tebl/C64-JoyKEY/gallery/2020-12-01 23.58.18.jpg

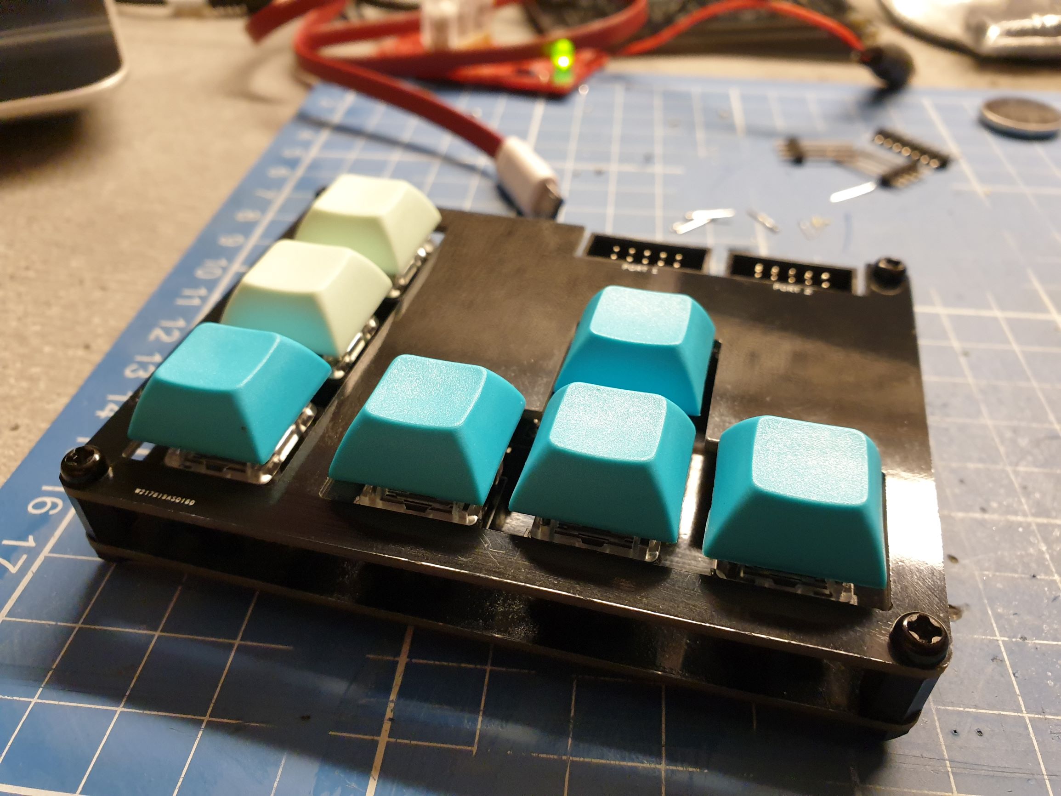
gallery/2020-12-01 23.58.18.jpg
