tebl/C64-JoyKEY/gallery/2020-12-05 21.04.29.jpg

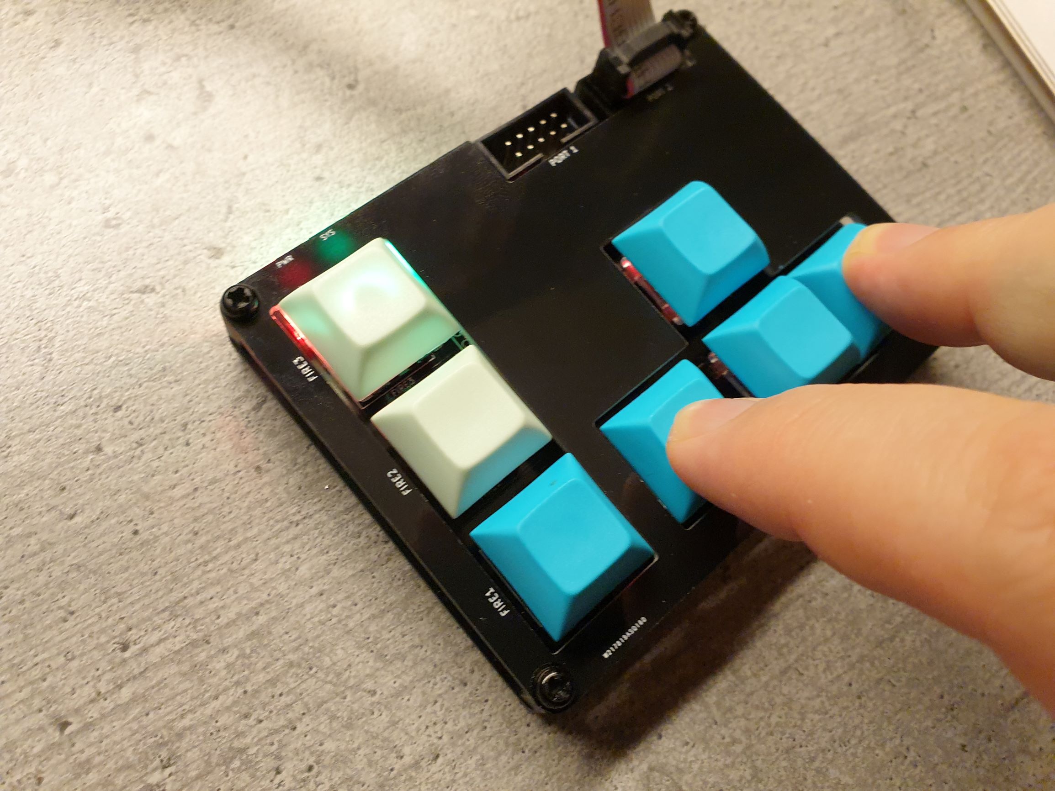
gallery/2020-12-05 21.04.29.jpg
