tebl/C64-JoyKEY/gallery/2020-12-06 00.33.15.jpg

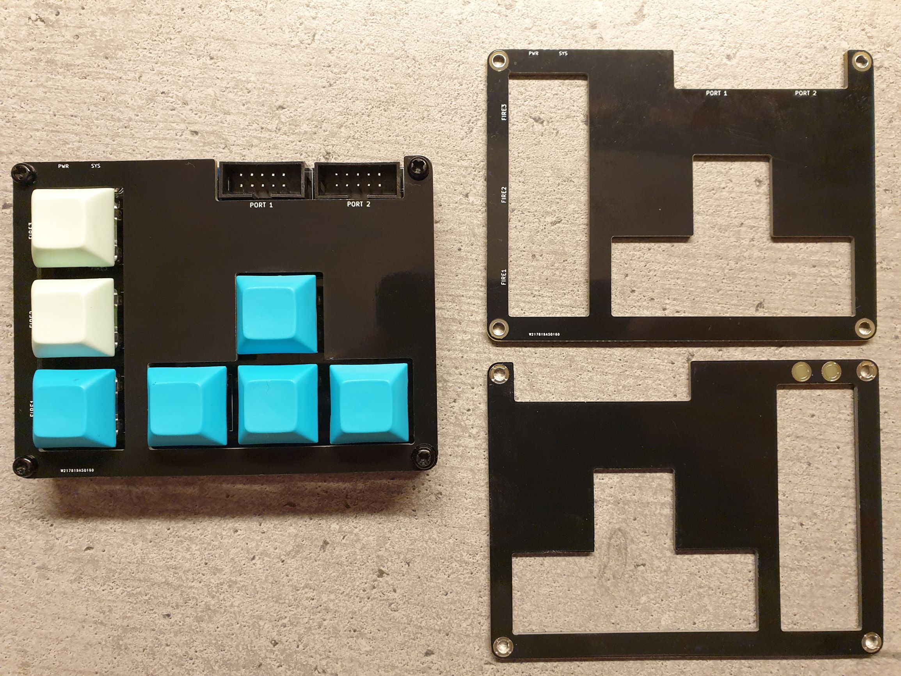
gallery/2020-12-06 00.33.15.jpg
