tebl/C64-JoyKEY/gallery/2021-01-07 00.18.26.jpg

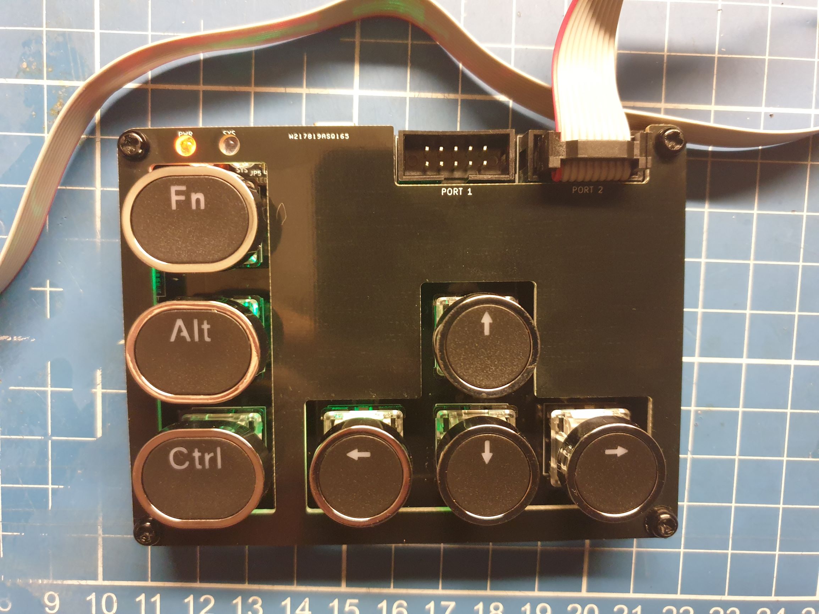
gallery/2021-01-07 00.18.26.jpg
