tebl/C64-JoyKEY/gallery/2021-01-18 20.31.05.jpg

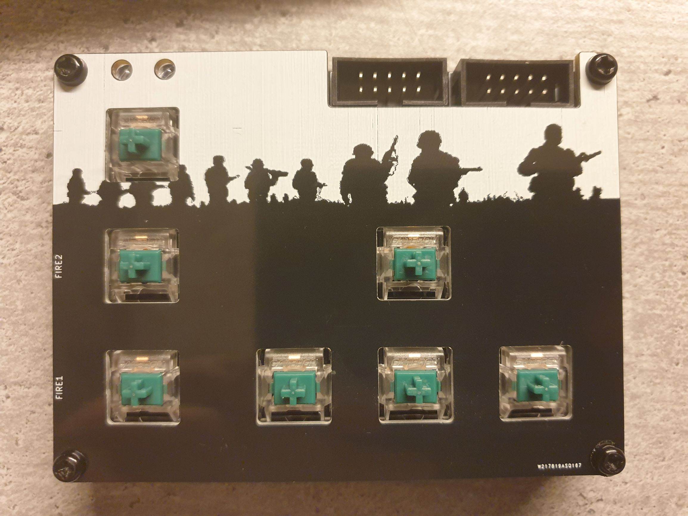
gallery/2021-01-18 20.31.05.jpg
