tebl/C64-JoyKEY/gallery/2021-01-18 20.33.16.jpg

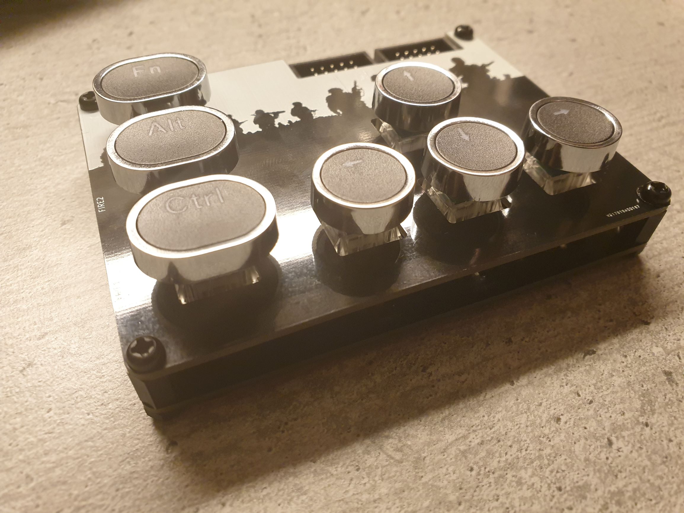
gallery/2021-01-18 20.33.16.jpg
