tebl/C64-JoyKEY/gallery/2021-01-26 00.23.01.jpg

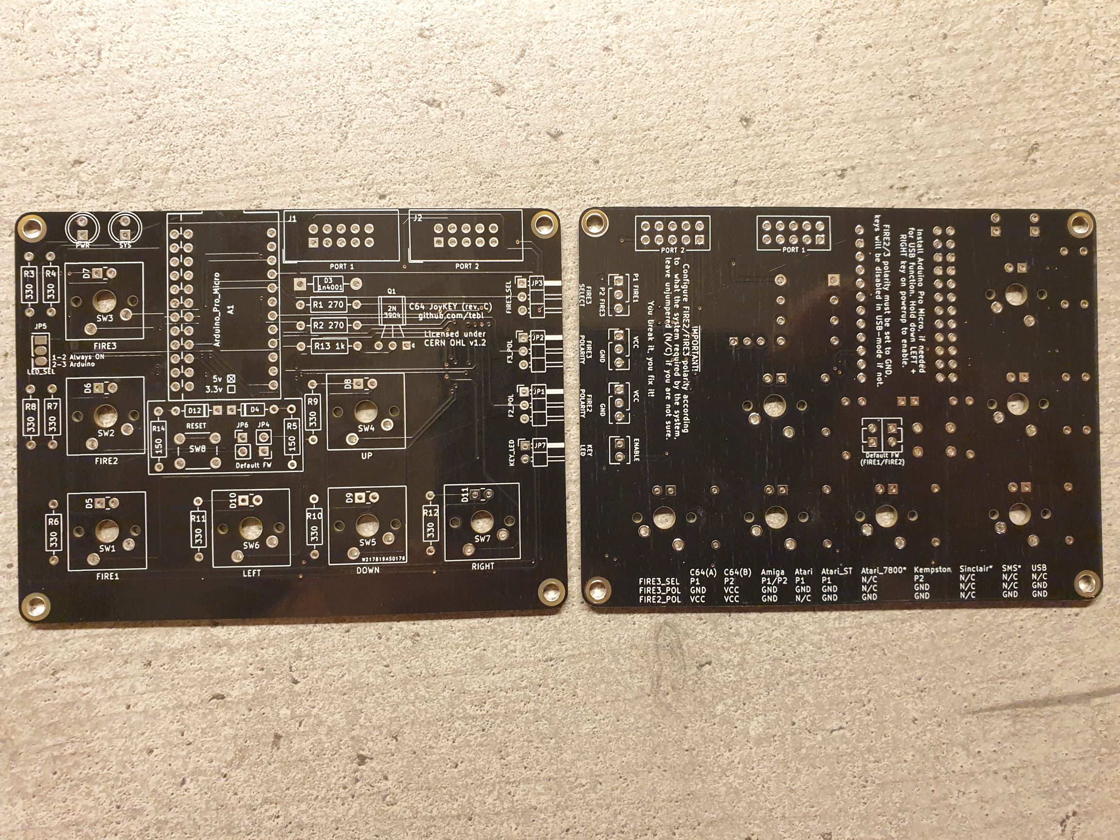
gallery/2021-01-26 00.23.01.jpg
