tebl/C64-JoyKEY/gallery/2021-01-26 03.19.31.jpg

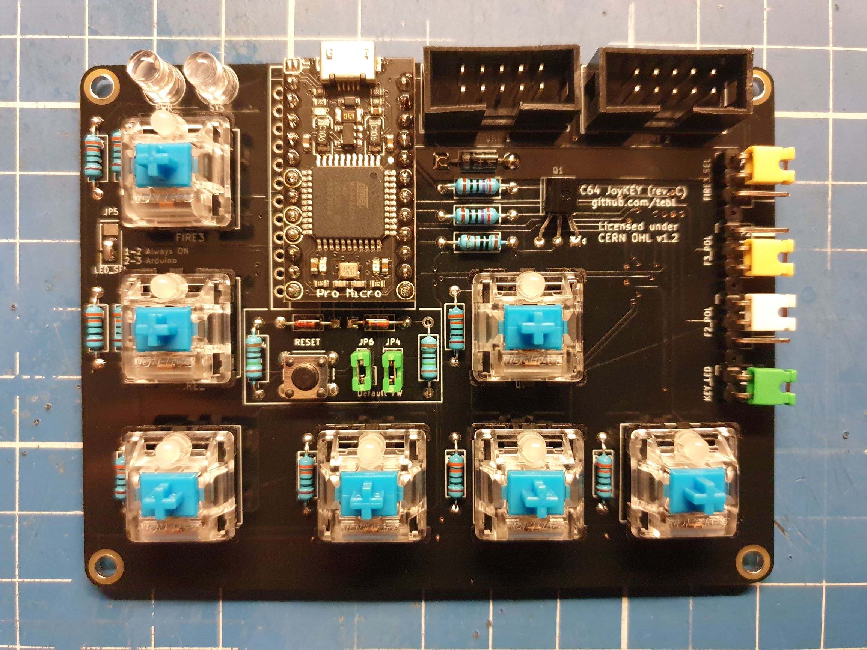
gallery/2021-01-26 03.19.31.jpg
