tebl/C64-JoyKEY/gallery/2021-02-02 23.40.10.jpg

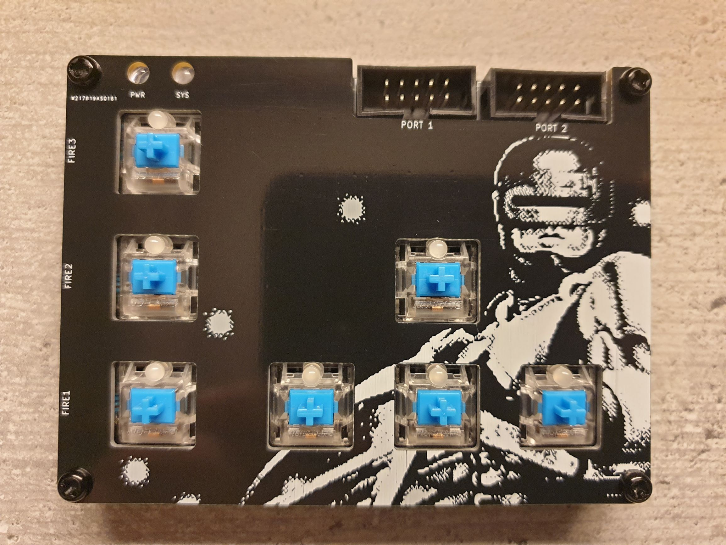
gallery/2021-02-02 23.40.10.jpg
