tebl/C64-JoyKEY/gallery/2021-02-02 23.41.32.jpg

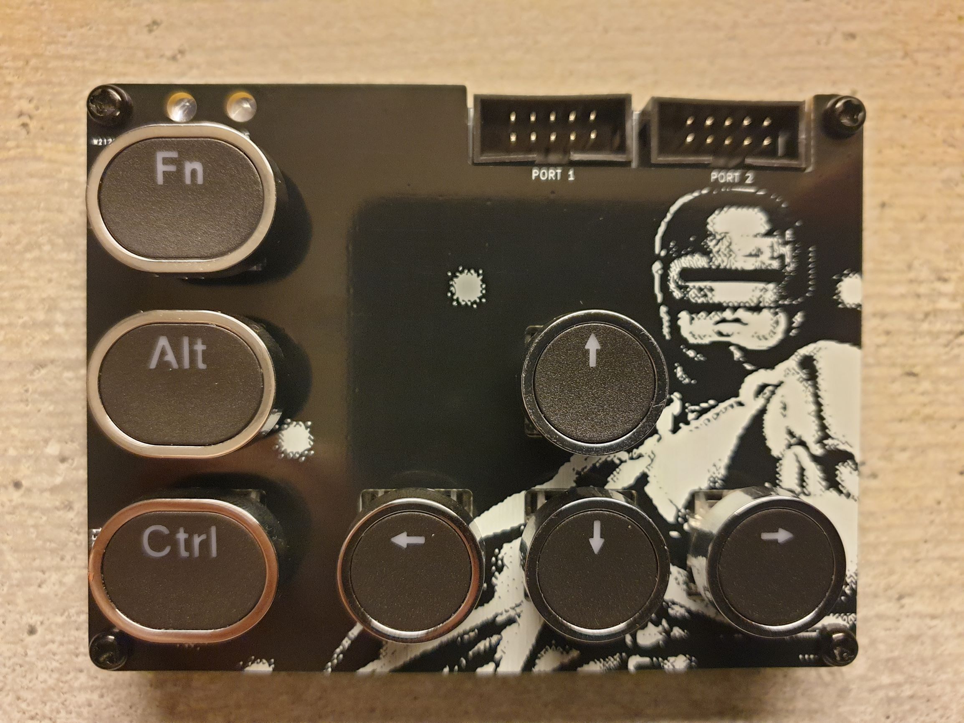
gallery/2021-02-02 23.41.32.jpg
