tebl/C64-JoyKEY/gallery/2021-02-03 00.52.26.jpg

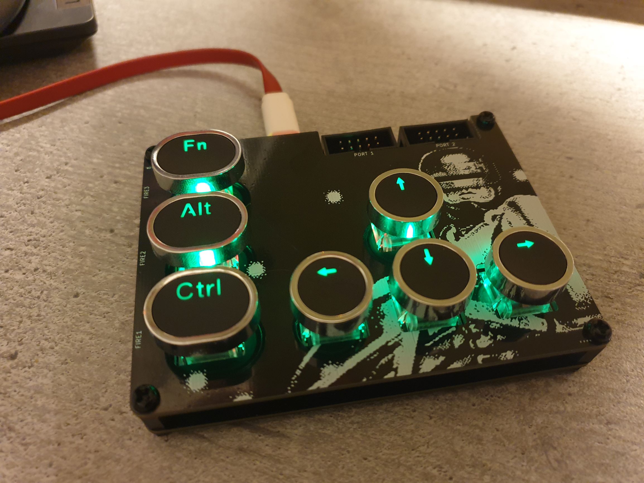
gallery/2021-02-03 00.52.26.jpg
