tebl/C64-JoyKEY/gallery/2021-03-08 21.28.13.jpg

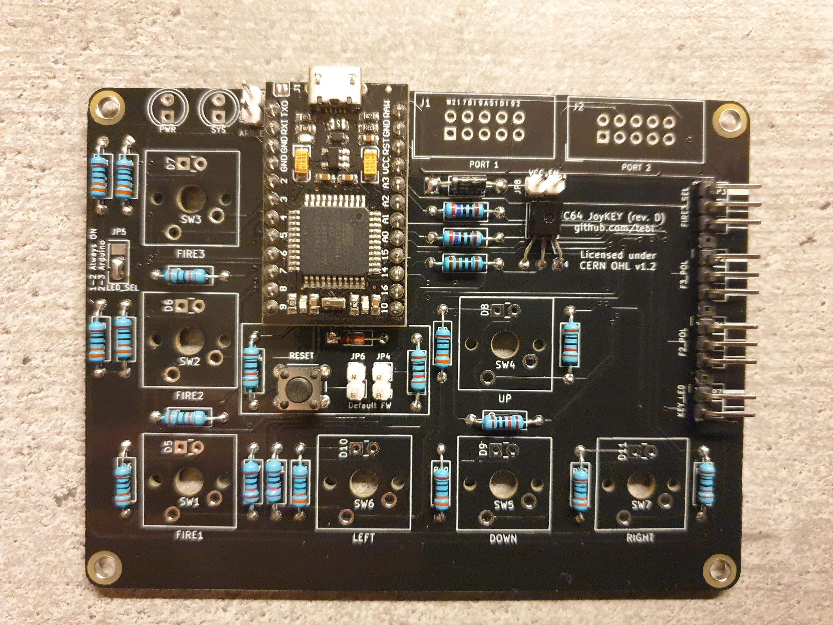
gallery/2021-03-08 21.28.13.jpg
