tebl/C64-JoyKEY/gallery/2021-03-09 01.28.27.jpg

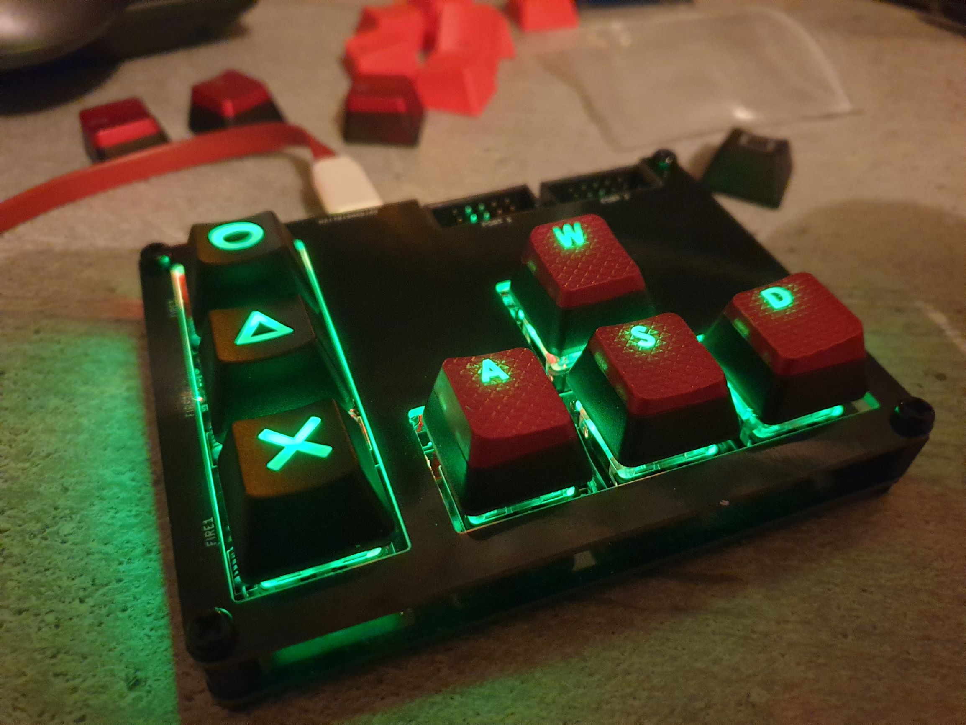
gallery/2021-03-09 01.28.27.jpg
