tebl/C64-JoyKEY/gallery/2021-03-09 01.42.43.jpg

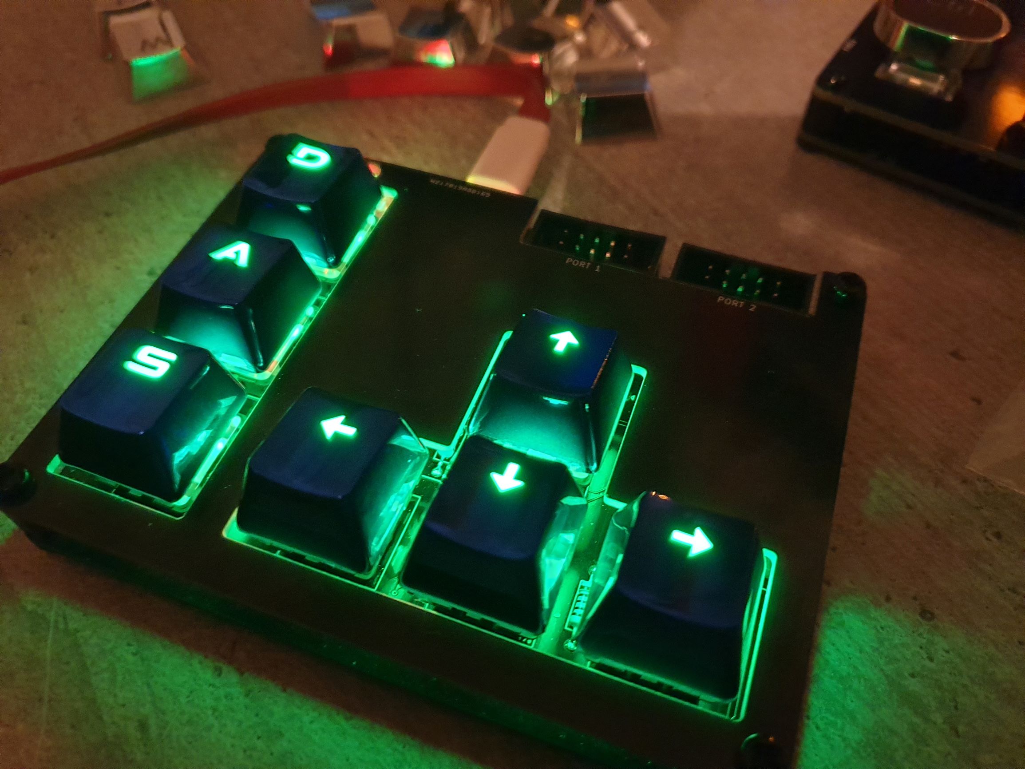
gallery/2021-03-09 01.42.43.jpg
