tebl/C64-JoyKEY/gallery/2021-03-10 20.38.43.jpg

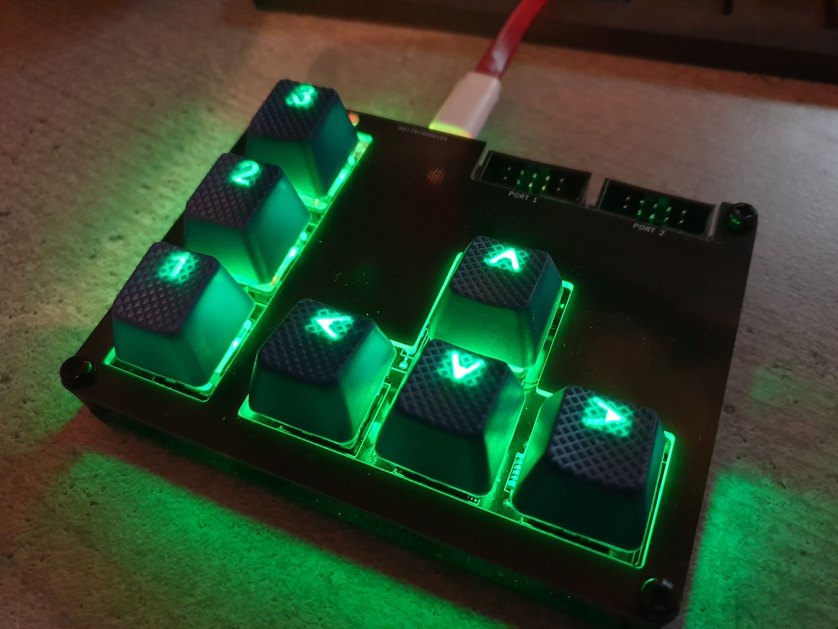
gallery/2021-03-10 20.38.43.jpg
