tebl/C64-JoyKEY/gallery/2021-03-30 01.16.27.jpg

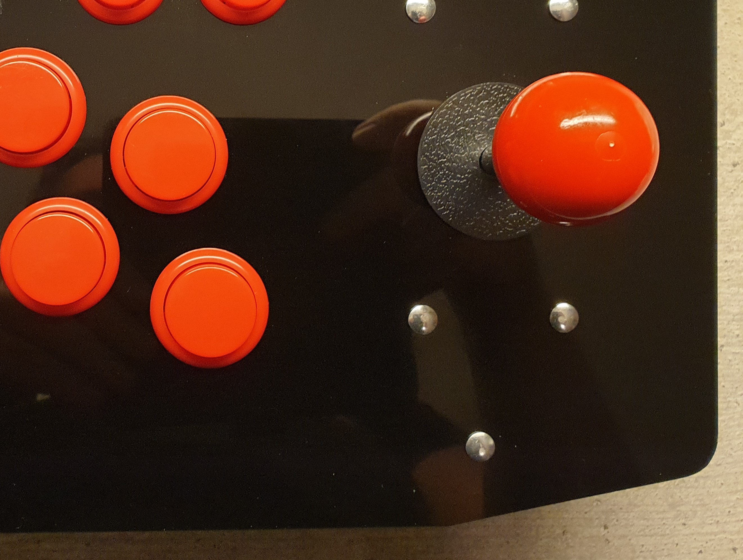
gallery/2021-03-30 01.16.27.jpg
