tebl/C64-JoyKEY/gallery/2021-04-14 00.00.06.jpg

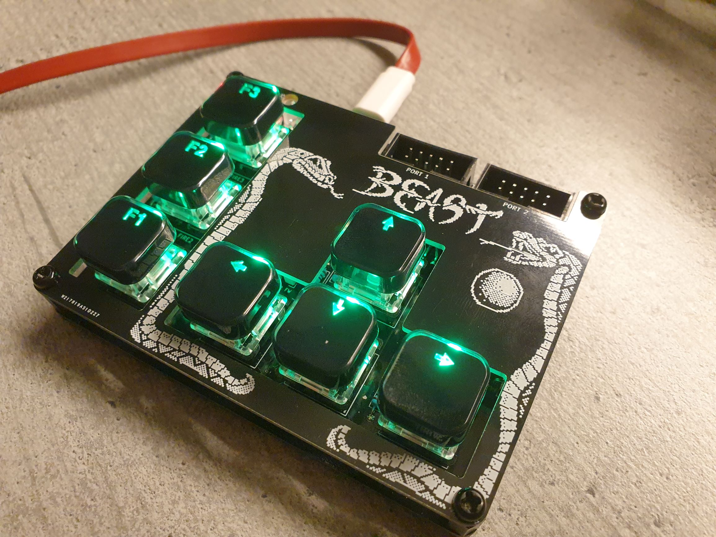
gallery/2021-04-14 00.00.06.jpg
