tebl/C64-JoyKEY/gallery/2022-02-19 15.27.10.jpg

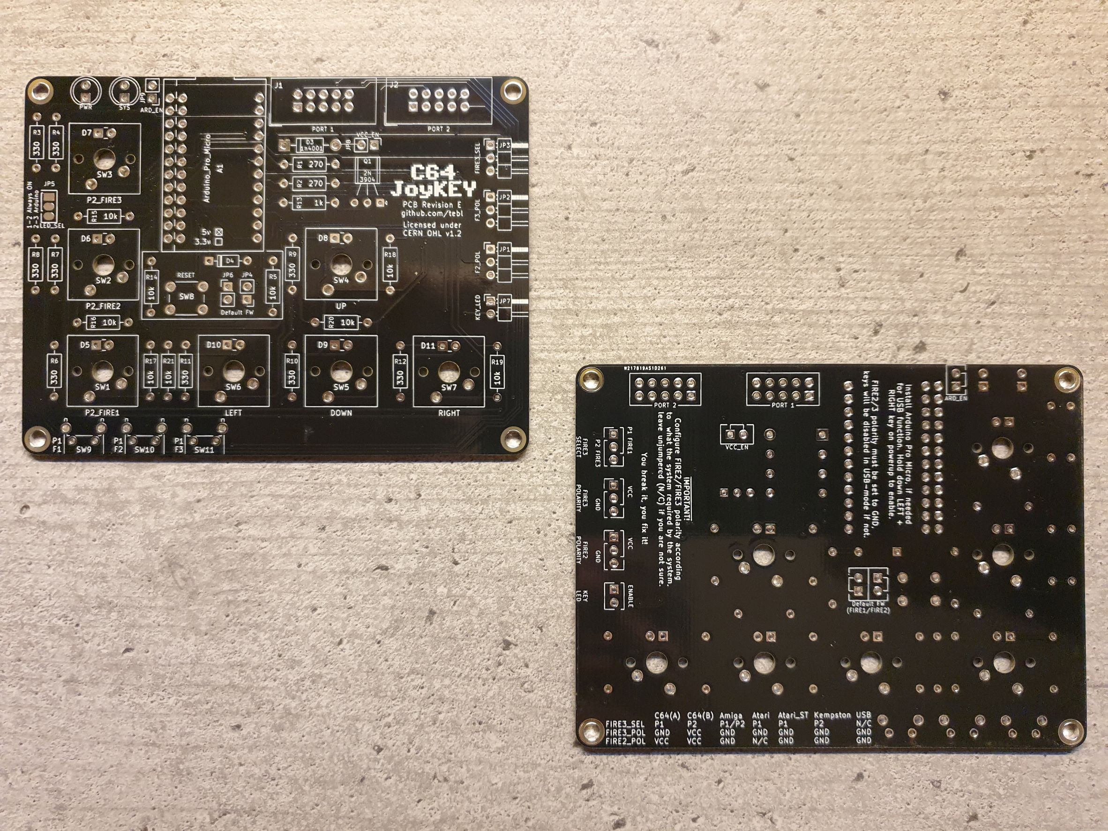
gallery/2022-02-19 15.27.10.jpg
