tebl/C64-JoyKEY/gallery/2022-02-19 16.09.59.jpg

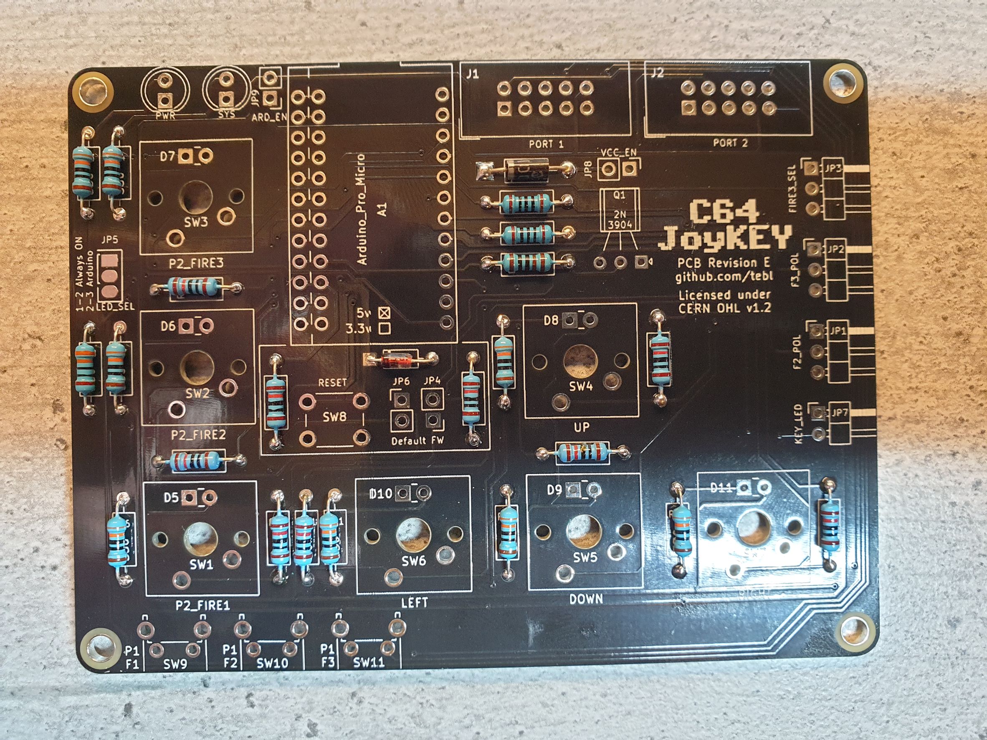
gallery/2022-02-19 16.09.59.jpg
