tebl/C64-JoyKEY/gallery/2022-02-19 16.12.47.jpg

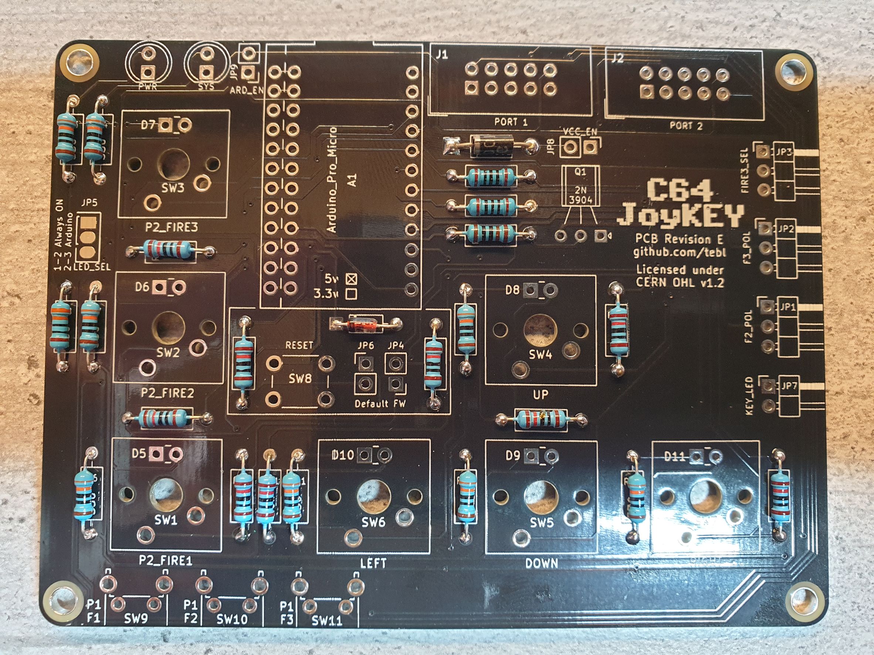
gallery/2022-02-19 16.12.47.jpg
