tebl/C64-JoyKEY/gallery/2022-02-19 16.19.15.jpg

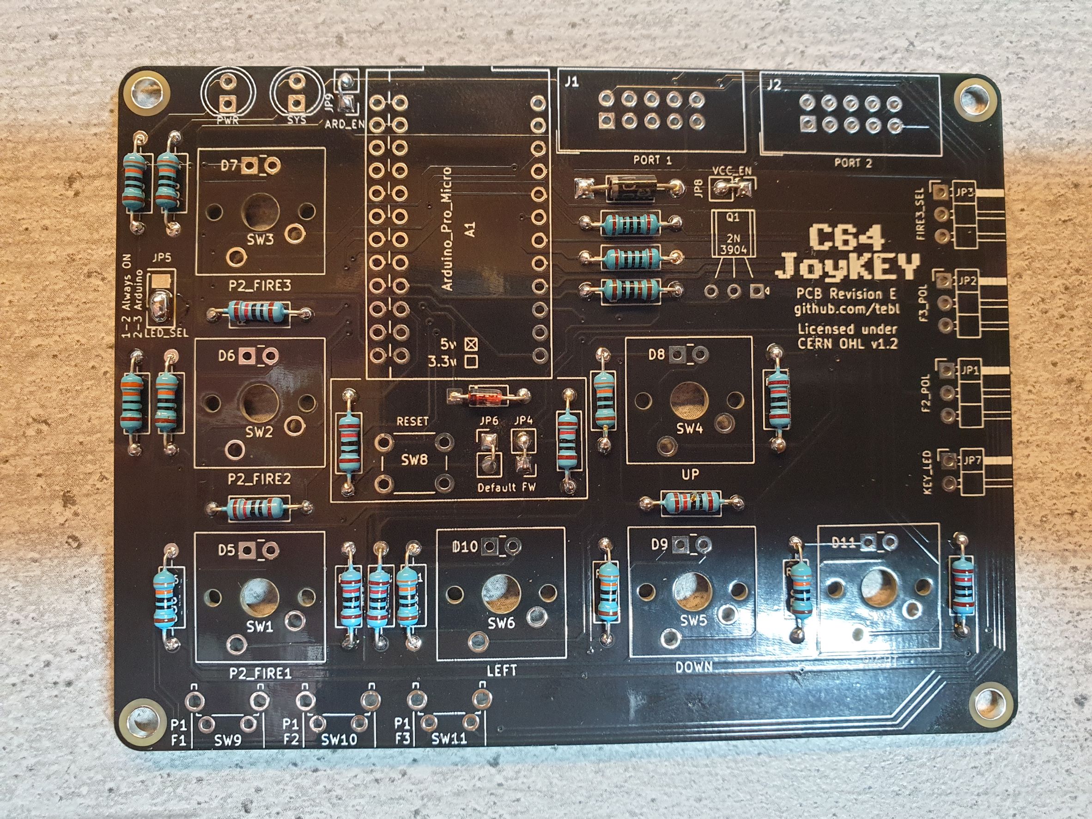
gallery/2022-02-19 16.19.15.jpg
