tebl/C64-JoyKEY/gallery/2022-02-19 16.20.50.jpg

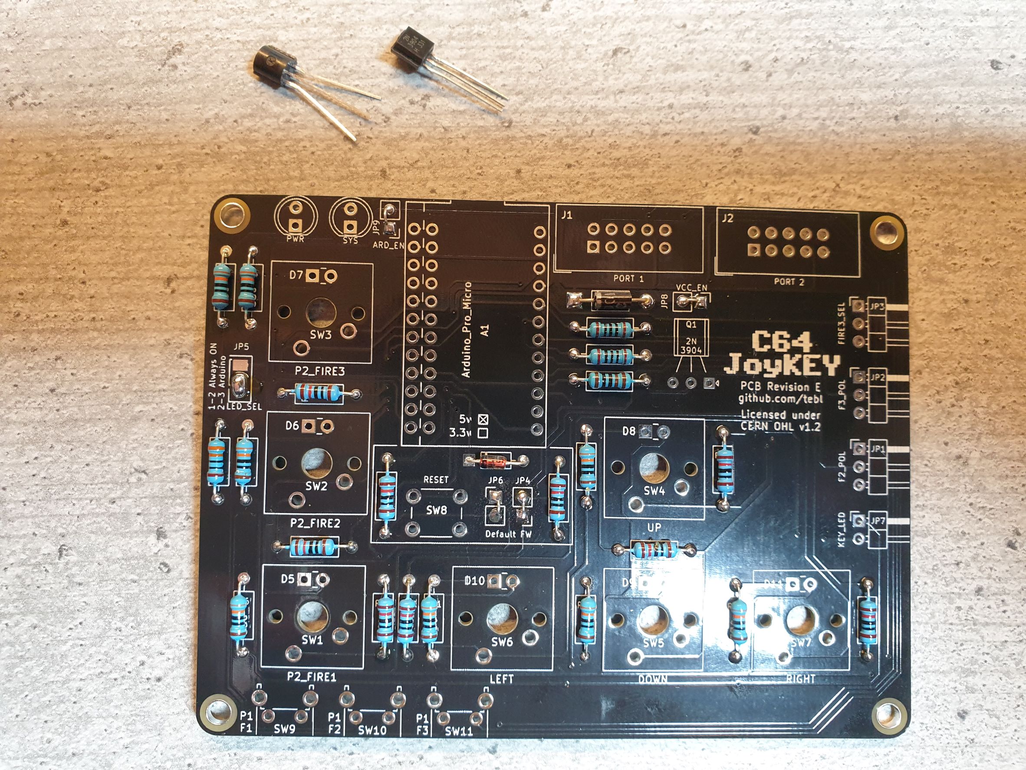
gallery/2022-02-19 16.20.50.jpg
