tebl/C64-JoyKEY/gallery/2022-02-19 16.23.03.jpg

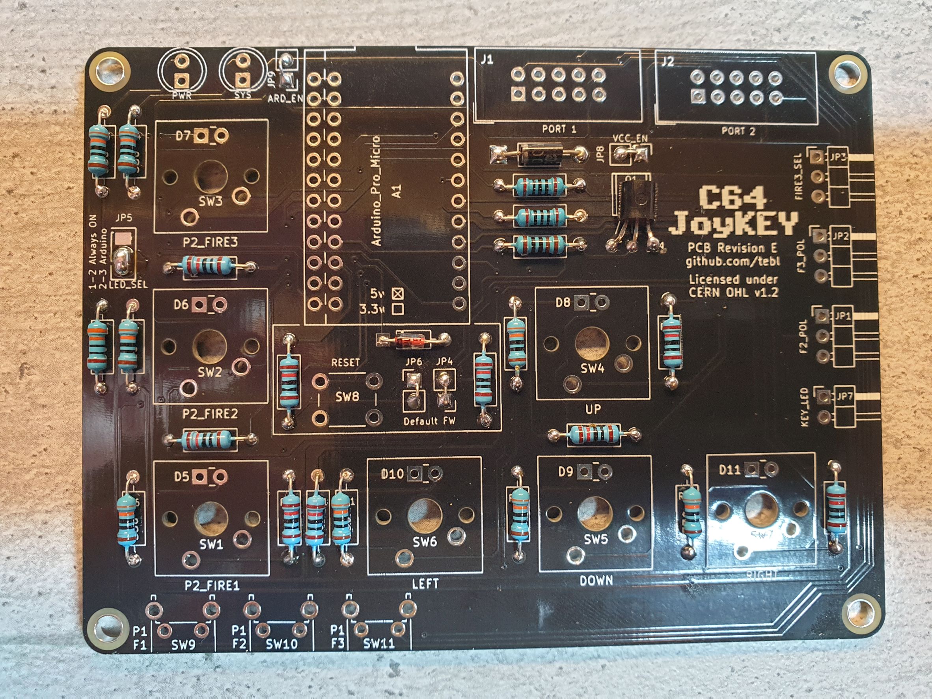
gallery/2022-02-19 16.23.03.jpg
