tebl/C64-JoyKEY/gallery/2022-02-19 16.27.23.jpg

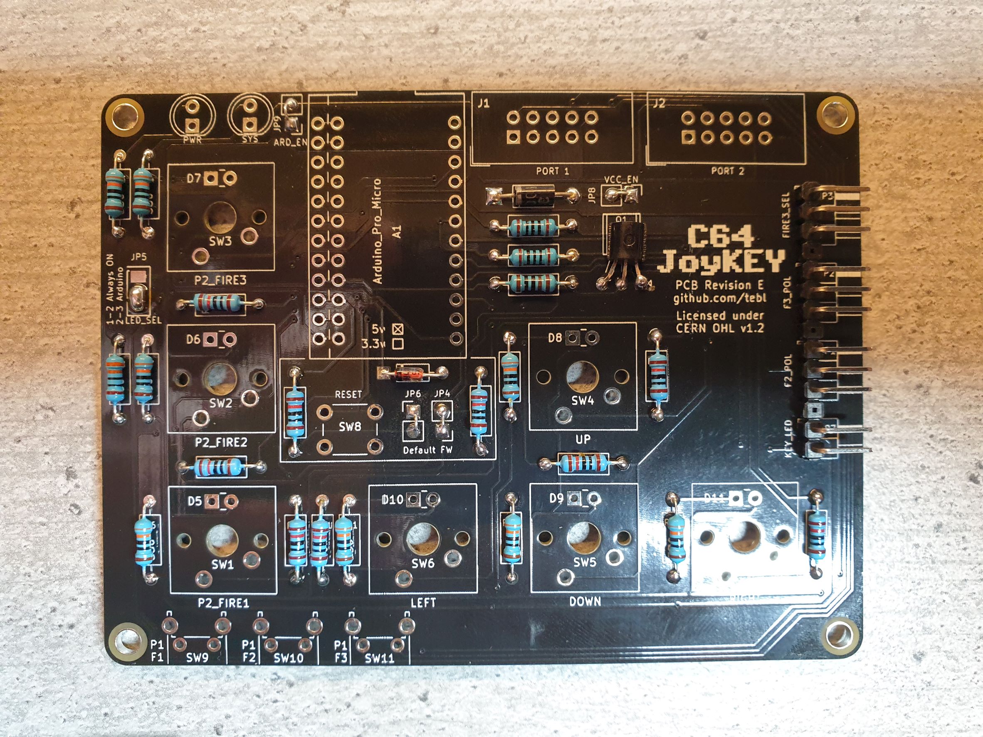
gallery/2022-02-19 16.27.23.jpg
