tebl/C64-JoyKEY/gallery/2022-02-19 16.37.38.jpg

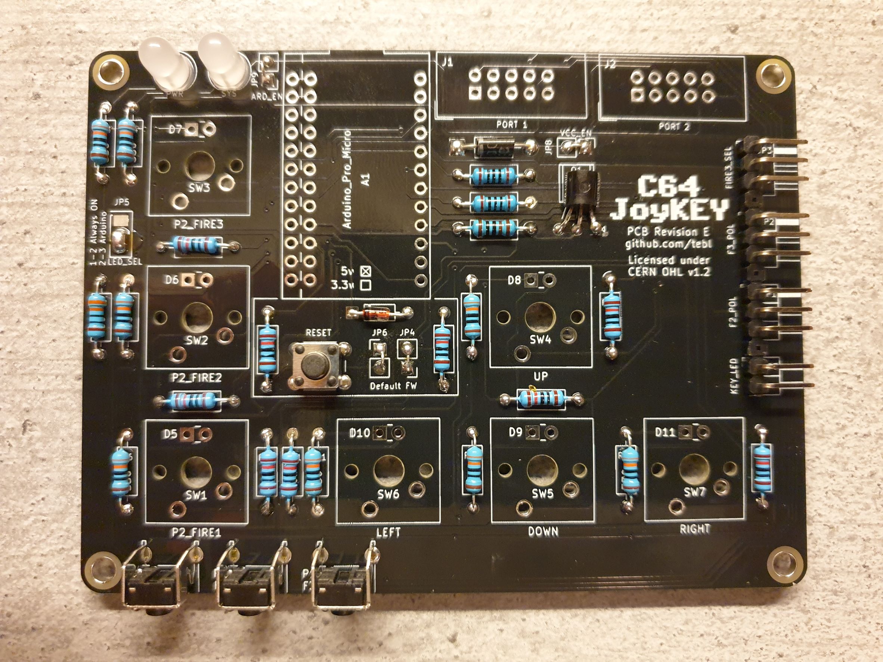
gallery/2022-02-19 16.37.38.jpg
