tebl/C64-JoyKEY/gallery/2022-02-19 16.48.18.jpg

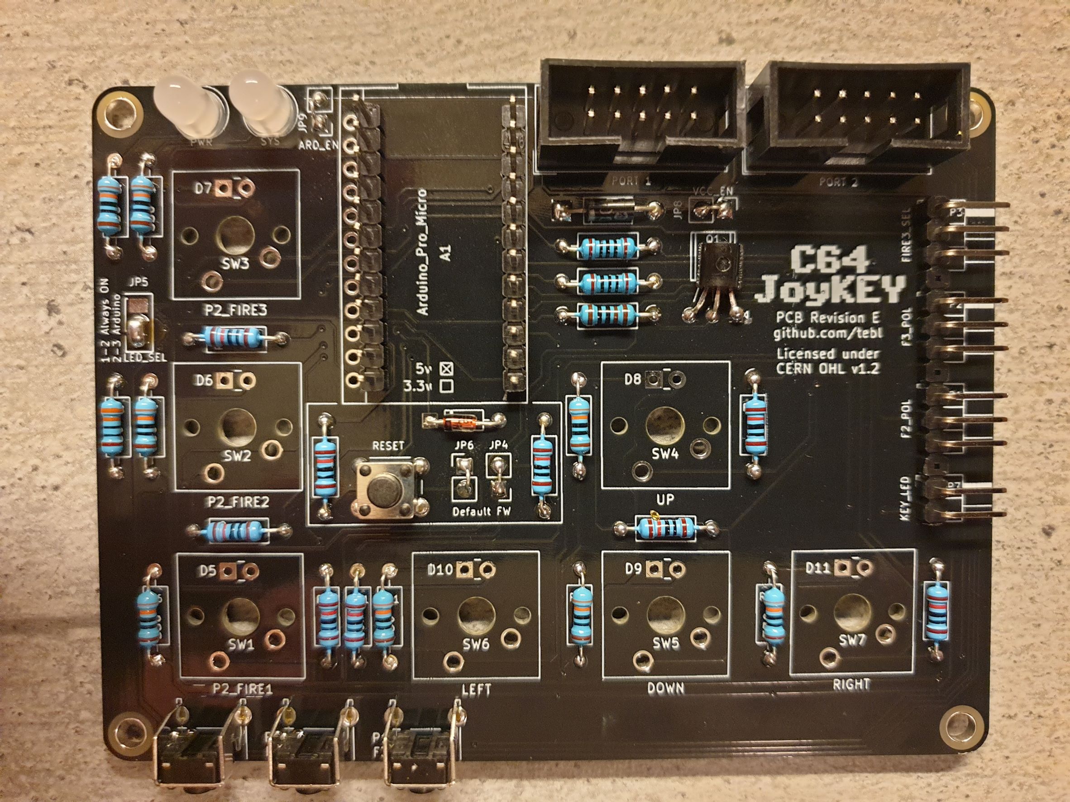
gallery/2022-02-19 16.48.18.jpg
