tebl/C64-JoyKEY/gallery/2022-02-19 17.05.05.jpg

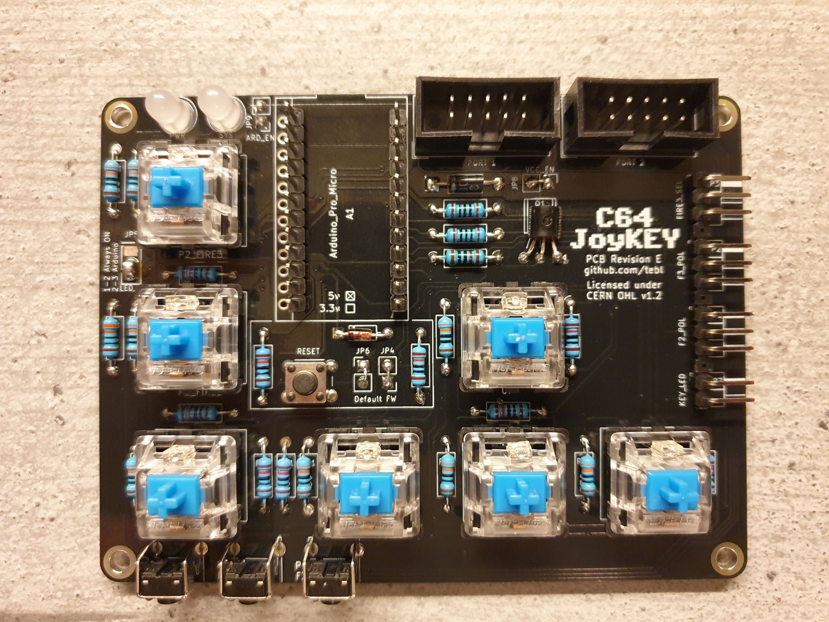
gallery/2022-02-19 17.05.05.jpg
