tebl/C64-JoyKEY/gallery/2022-02-19 17.21.17.jpg

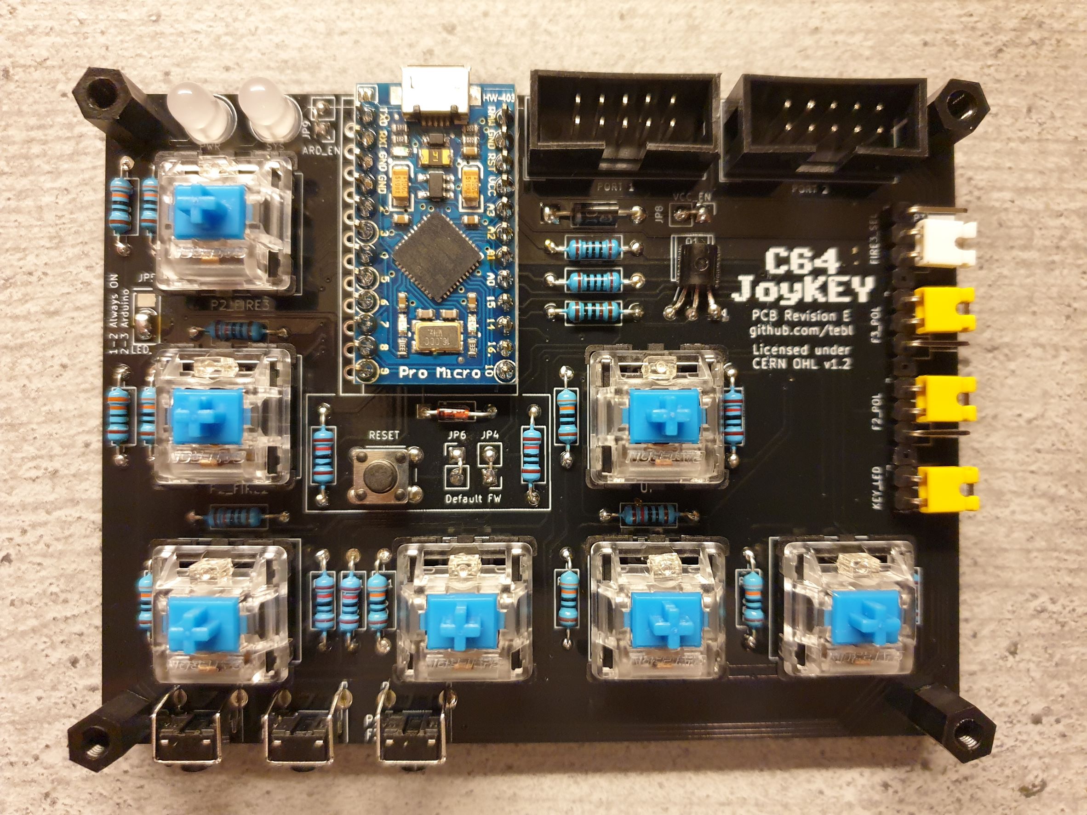
gallery/2022-02-19 17.21.17.jpg
