tebl/C64-JoyKEY/gallery/2022-02-19 17.38.39.jpg

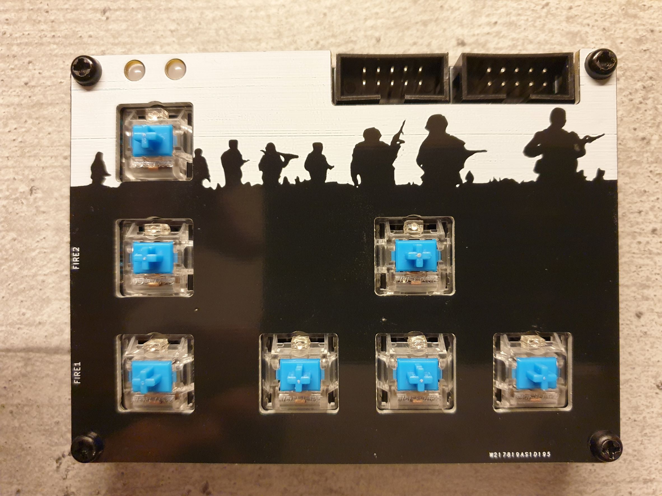
gallery/2022-02-19 17.38.39.jpg
