tebl/C64-JoyKEY/gallery/2022-02-19 17.41.41.jpg

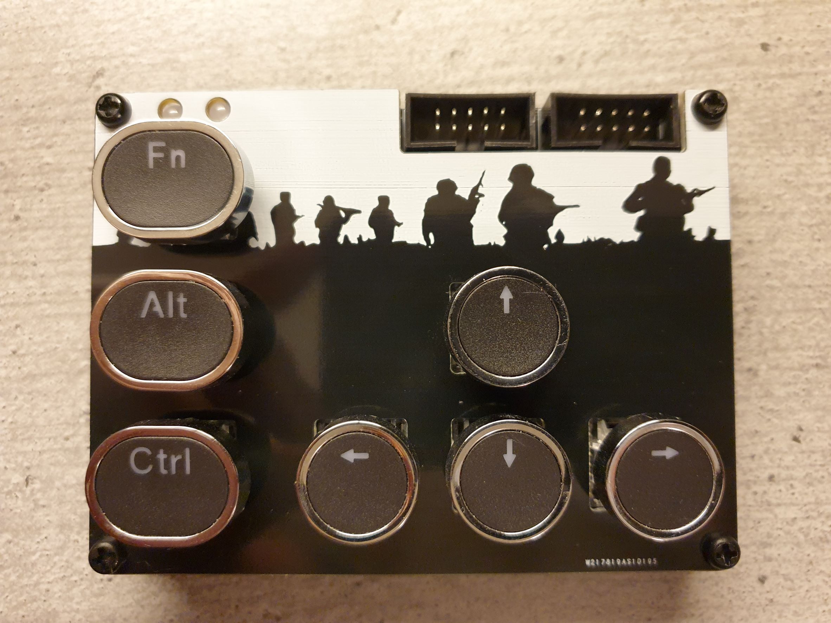
gallery/2022-02-19 17.41.41.jpg
