tebl/C64-JoyKEY/gallery/2024-11-01 03.02.20.jpg

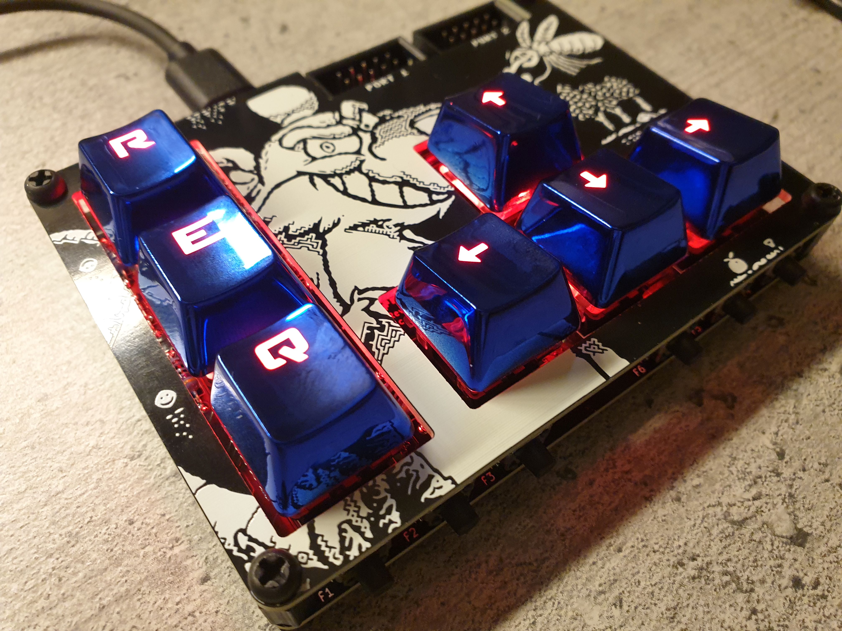
gallery/2024-11-01 03.02.20.jpg
