tebl/C64-JoyKEY/gallery/2024-11-20 01.26.48.jpg

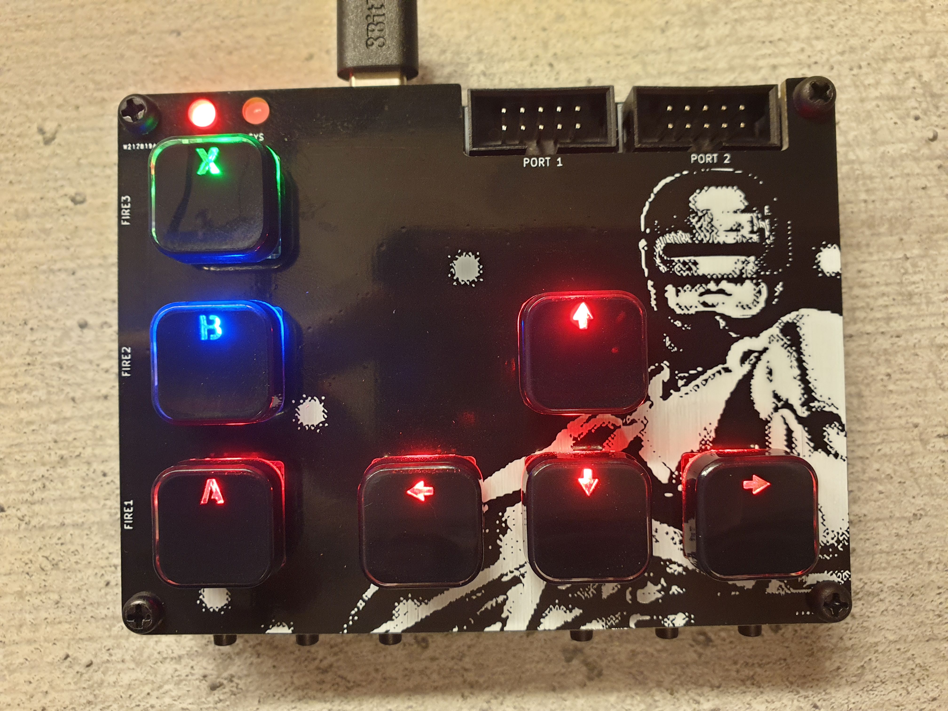
gallery/2024-11-20 01.26.48.jpg
