tebl/C64-JoyKEY/gallery/2024-11-20 01.27.16.jpg

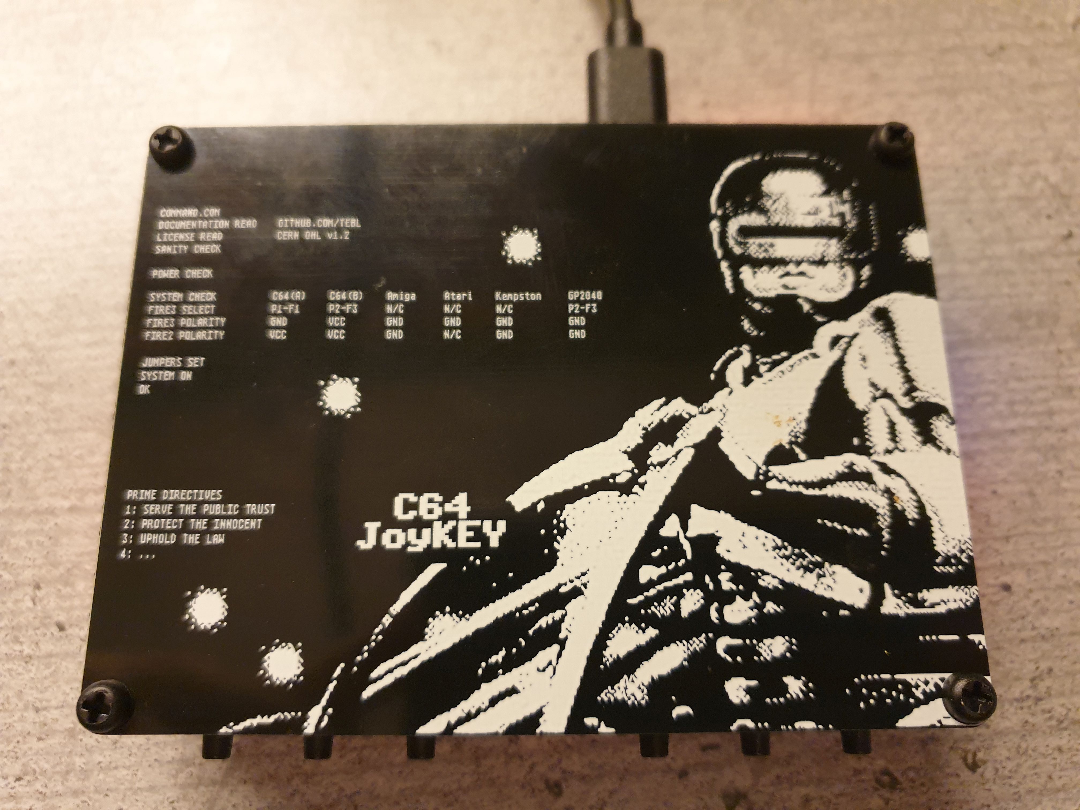
gallery/2024-11-20 01.27.16.jpg
