tebl/C64-JoyKEY/gallery/2024-11-22 02.50.10.jpg

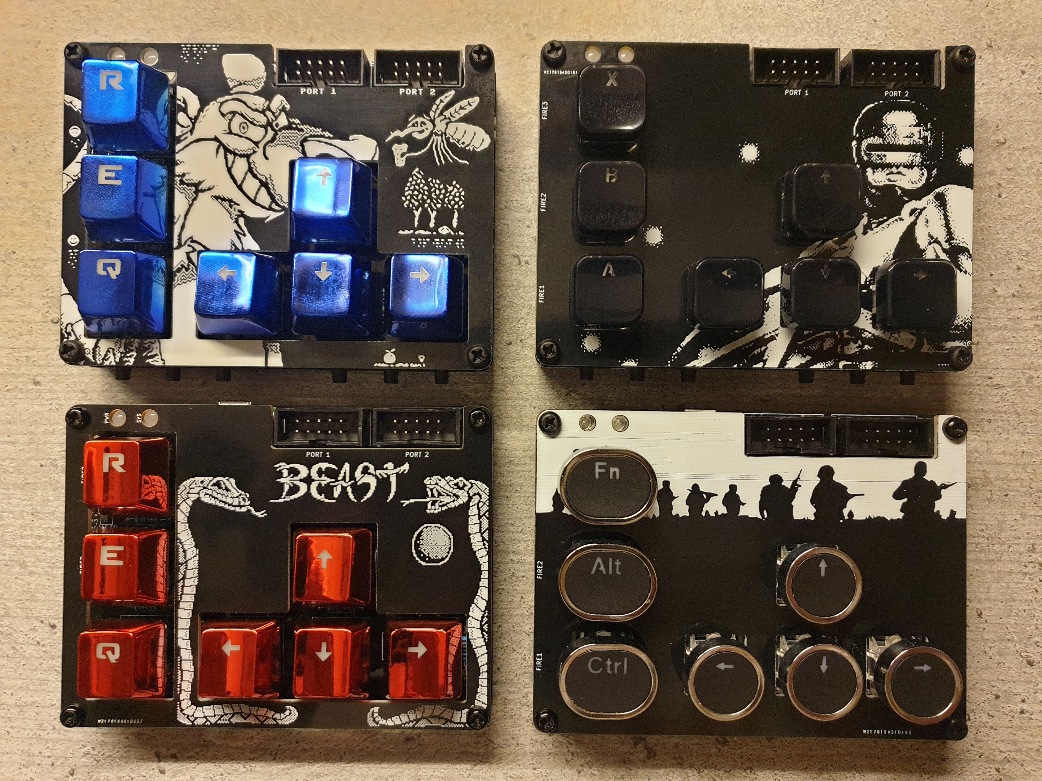
gallery/2024-11-22 02.50.10.jpg
