tebl/C64-JoyKEY/gallery/2024-12-19 22.20.43.jpg

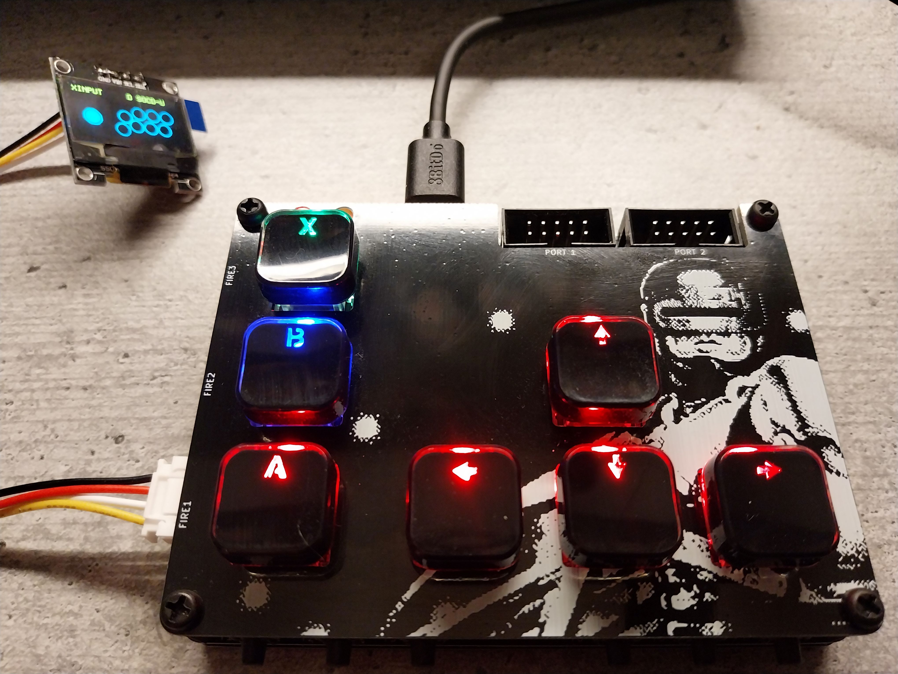
gallery/2024-12-19 22.20.43.jpg
