tebl/C64-JoyKEY/gallery/2024-12-20 00.54.49.jpg

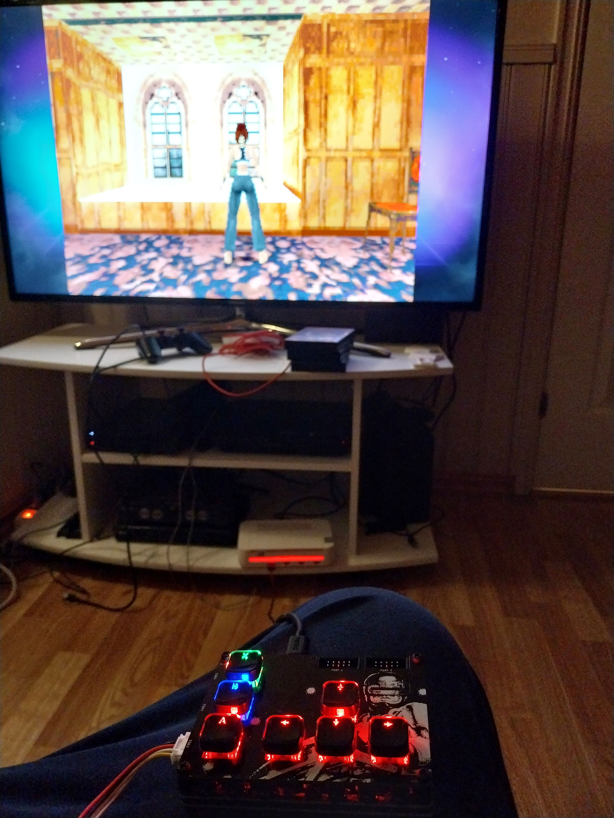
gallery/2024-12-20 00.54.49.jpg
