tebl/C64-JoyKEY/gallery/a8n_system.jpg

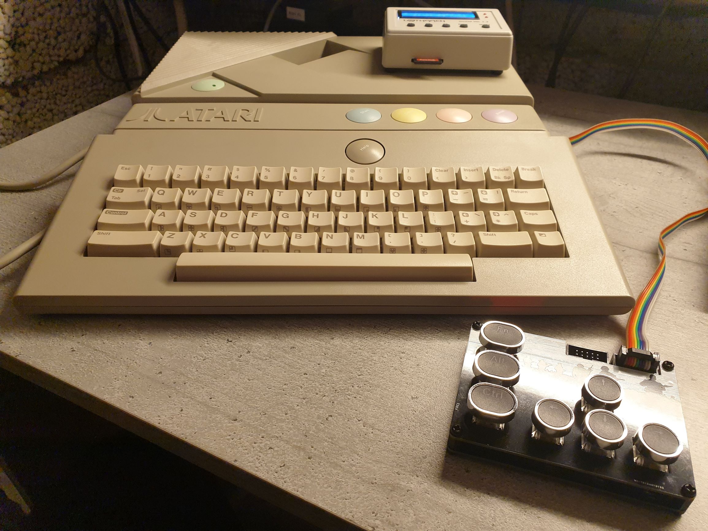
gallery/a8n_system.jpg
