tebl/C64-JoyKEY/gallery/Adapter 9 FaceplateB.jpg

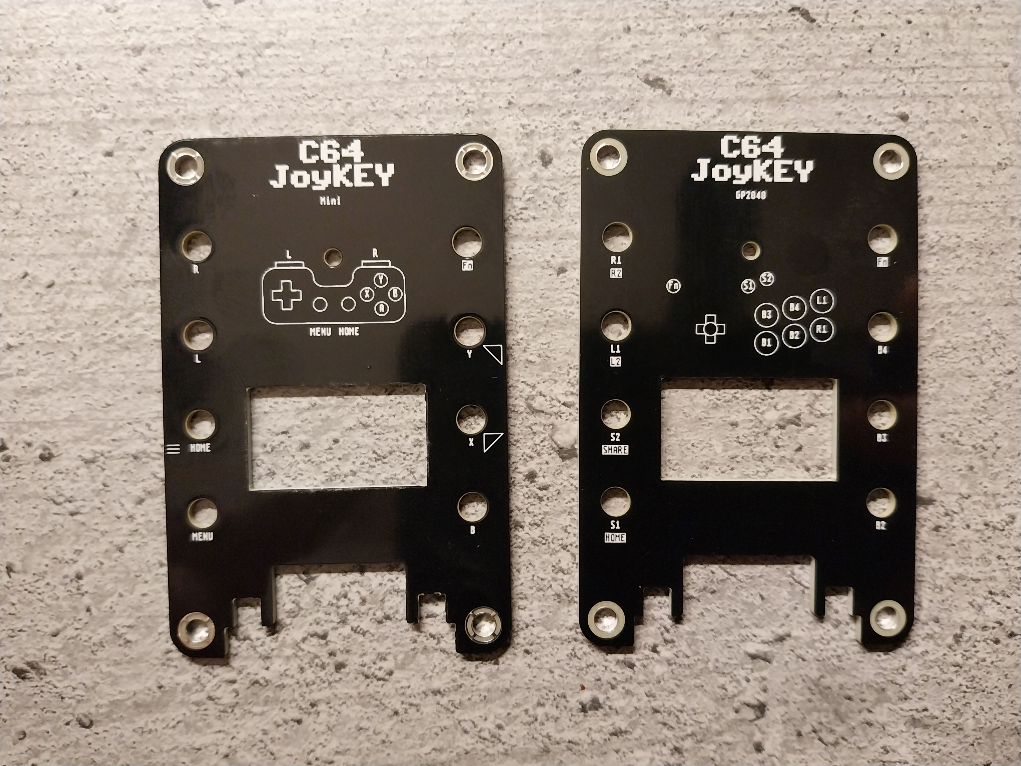
gallery/Adapter 9 FaceplateB.jpg
