tebl/C64-JoyKEY/gallery/Adapter 9 FaceplateB.png

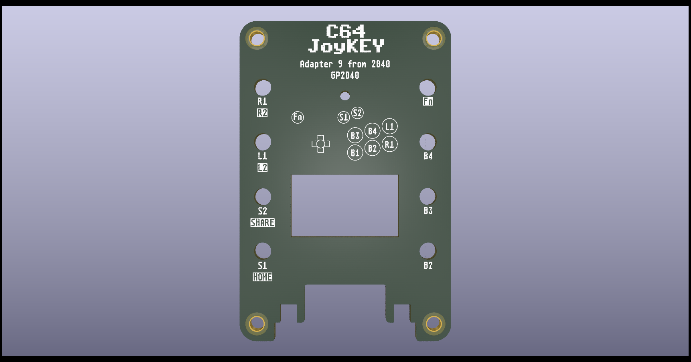
gallery/Adapter 9 FaceplateB.png
