tebl/C64-JoyKEY/gallery/Adapter 9 from 2040.png

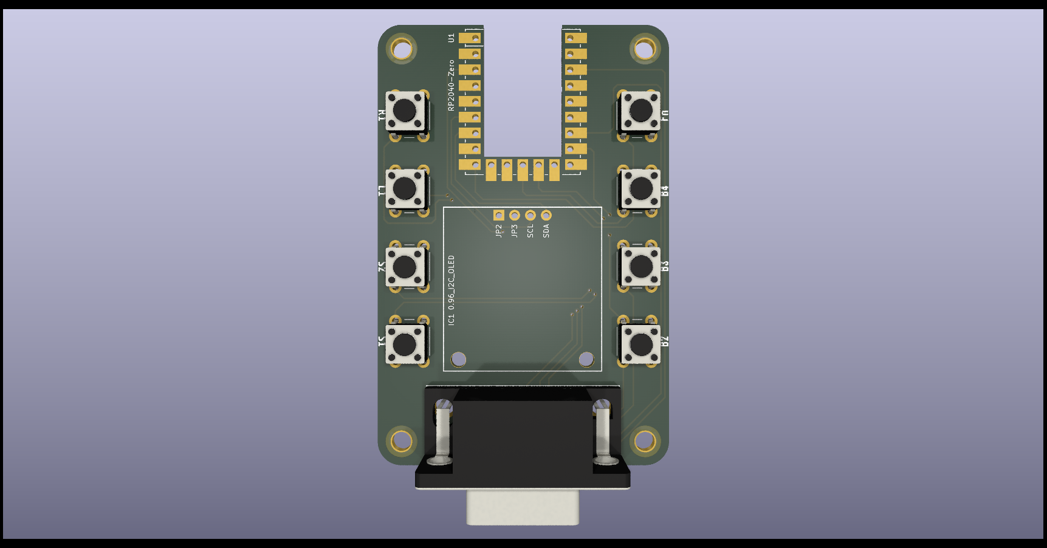
gallery/Adapter 9 from 2040.png
