tebl/C64-JoyKEY/gallery/amiga_system2.jpg

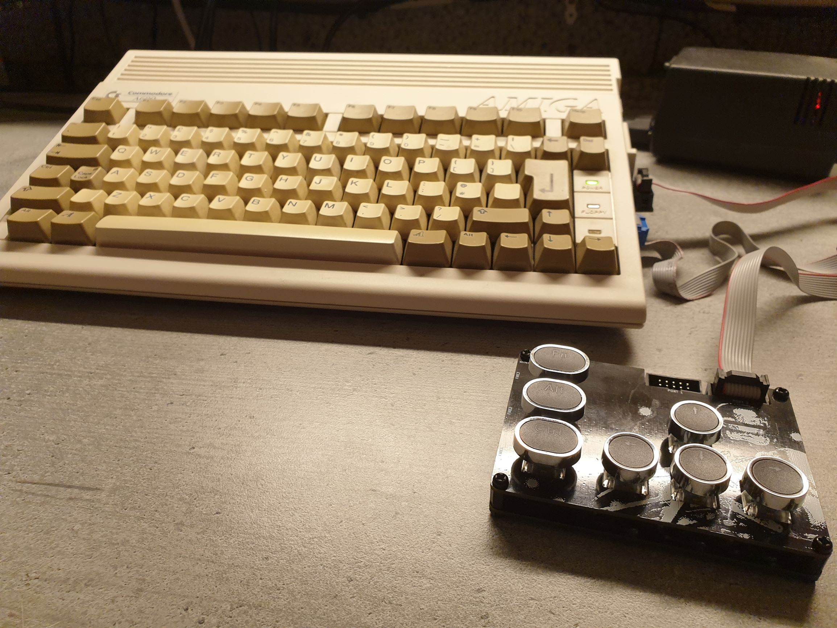
gallery/amiga_system2.jpg
