tebl/C64-JoyKEY/gallery/apple2e_adapter.jpg

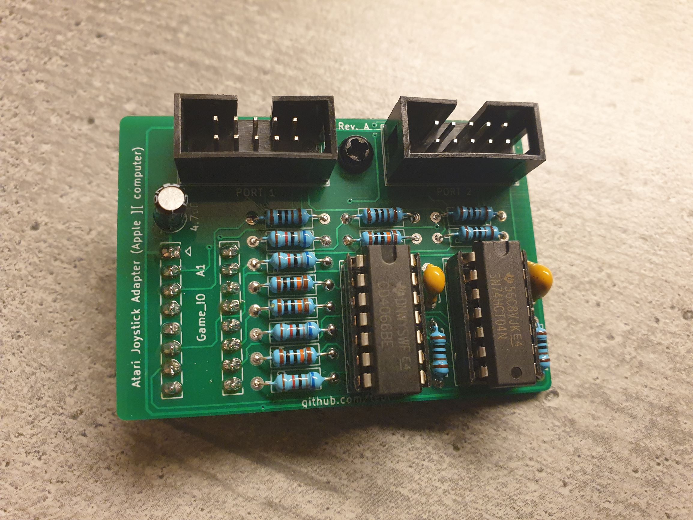
gallery/apple2e_adapter.jpg
