tebl/C64-JoyKEY/gallery/Arcade 2040.png

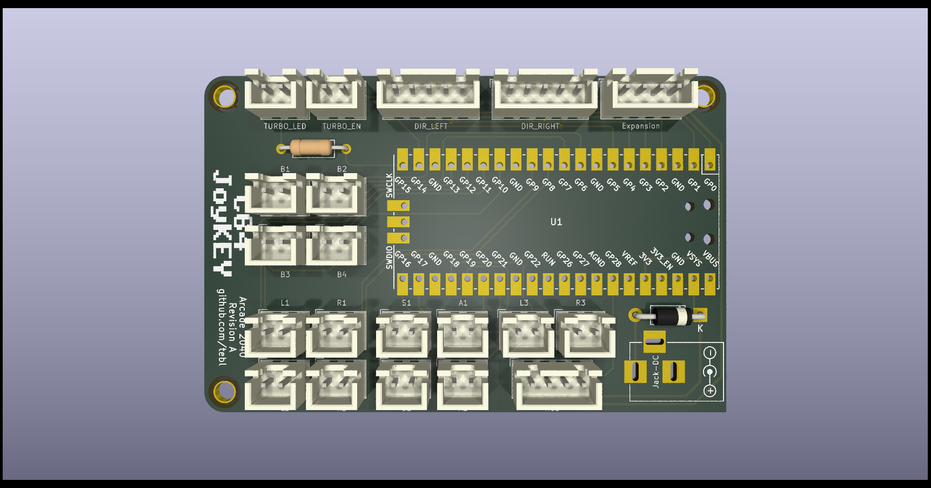
gallery/Arcade 2040.png
