tebl/C64-JoyKEY/gallery/C64 Arcade Preview.png

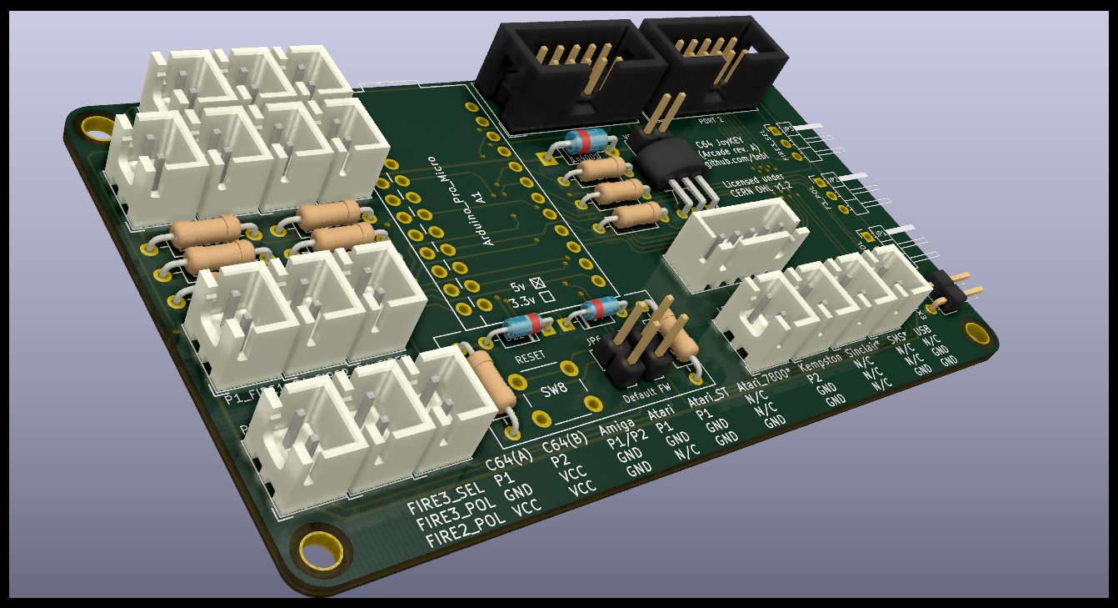
gallery/C64 Arcade Preview.png
