tebl/C64-JoyKEY/gallery/C64 Joykey 2040.png

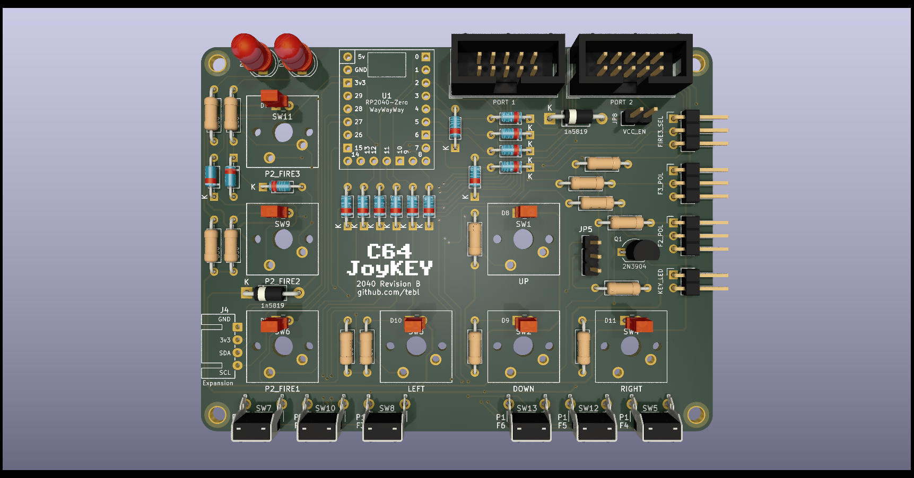
gallery/C64 Joykey 2040.png
