tebl/C64-JoyKEY/gallery/C64 Joykey Faceplate X1 (top).png

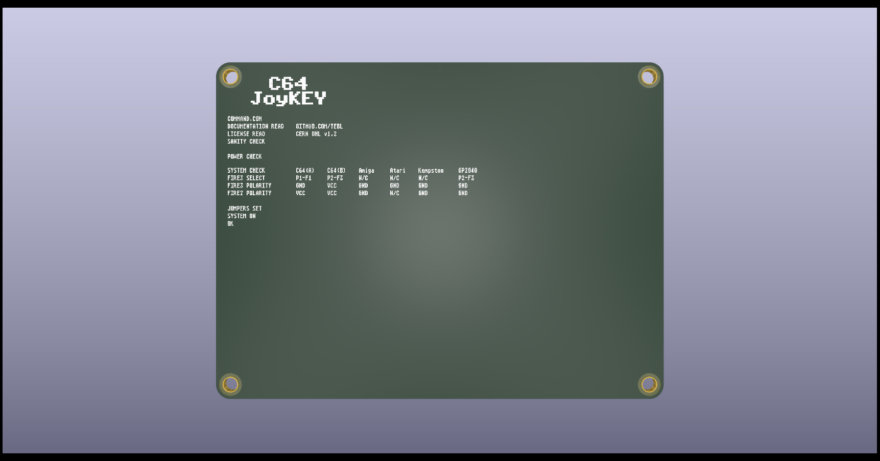
gallery/C64 Joykey Faceplate X1 (top).png
