tebl/C64-JoyKEY/gallery/C64 Joykey Faceplate X1.png

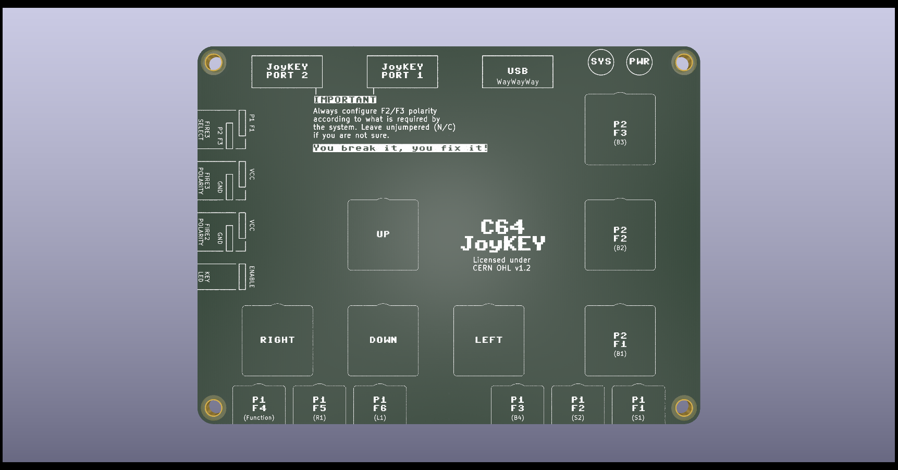
gallery/C64 Joykey Faceplate X1.png
