tebl/C64-JoyKEY/gallery/C64 Joykey.png

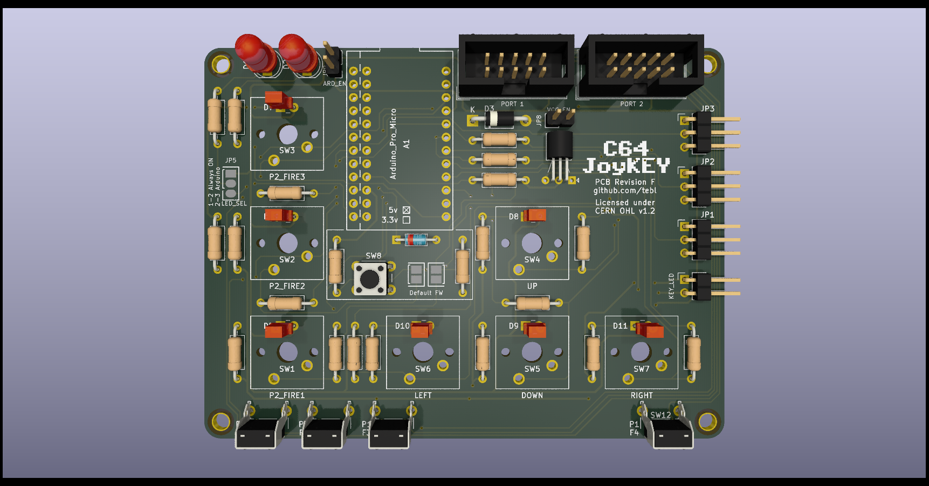
gallery/C64 Joykey.png
