tebl/C64-JoyKEY/gallery/Gameport.png

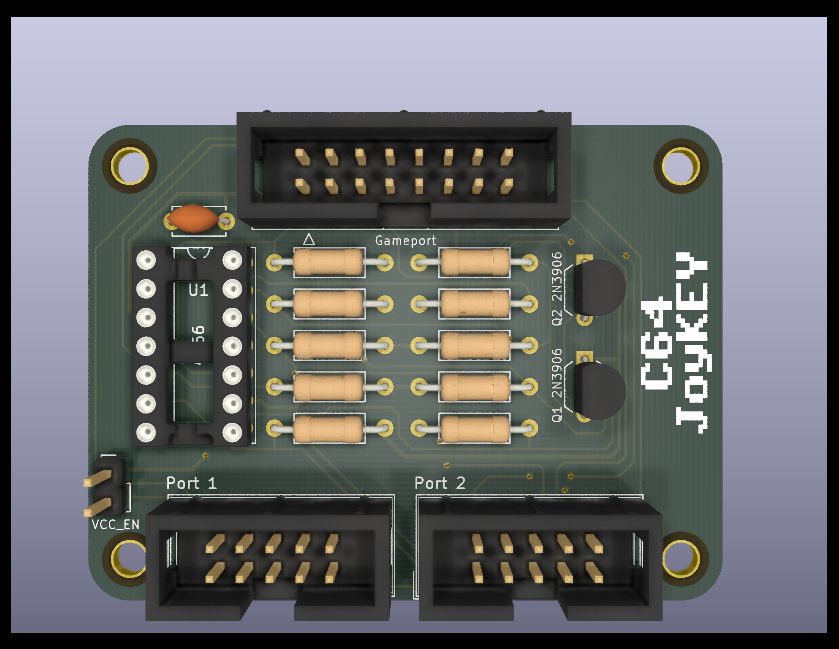
gallery/Gameport.png
