tebl/C64-JoyKEY/gallery/gp2040/rp2040-zero/system_stats.png

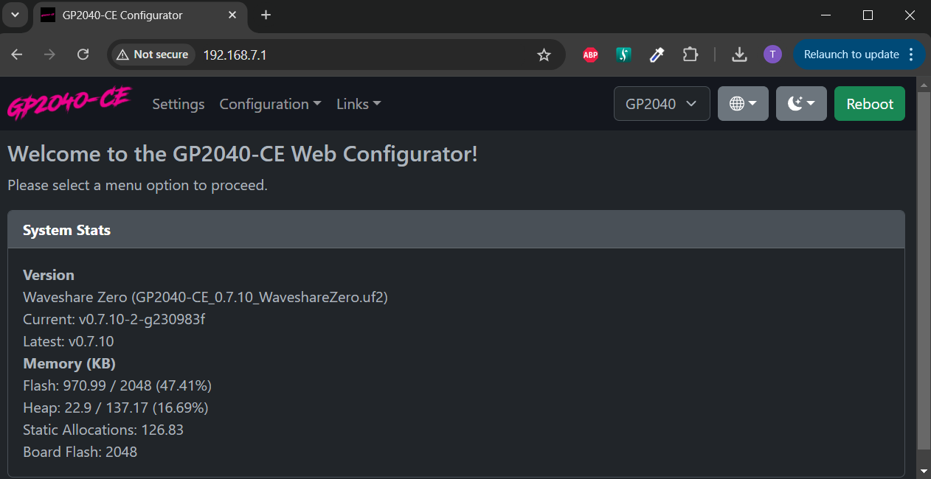
gallery/gp2040/rp2040-zero/system_stats.png
