tebl/C64-JoyKEY/gallery/gp2040/rp2040-zero/the_c64_reference.png

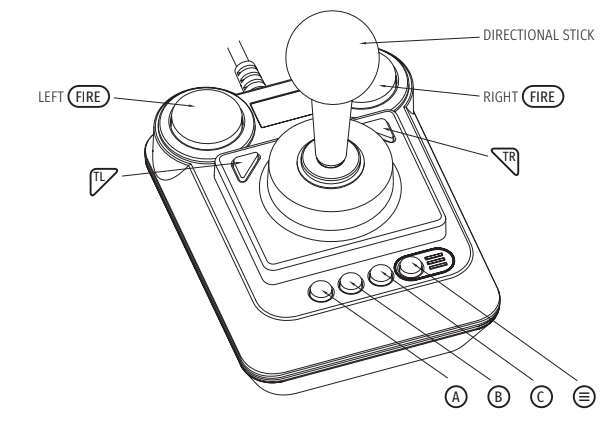
gallery/gp2040/rp2040-zero/the_c64_reference.png
