tebl/C64-JoyKEY/gallery/kempston_system.jpg

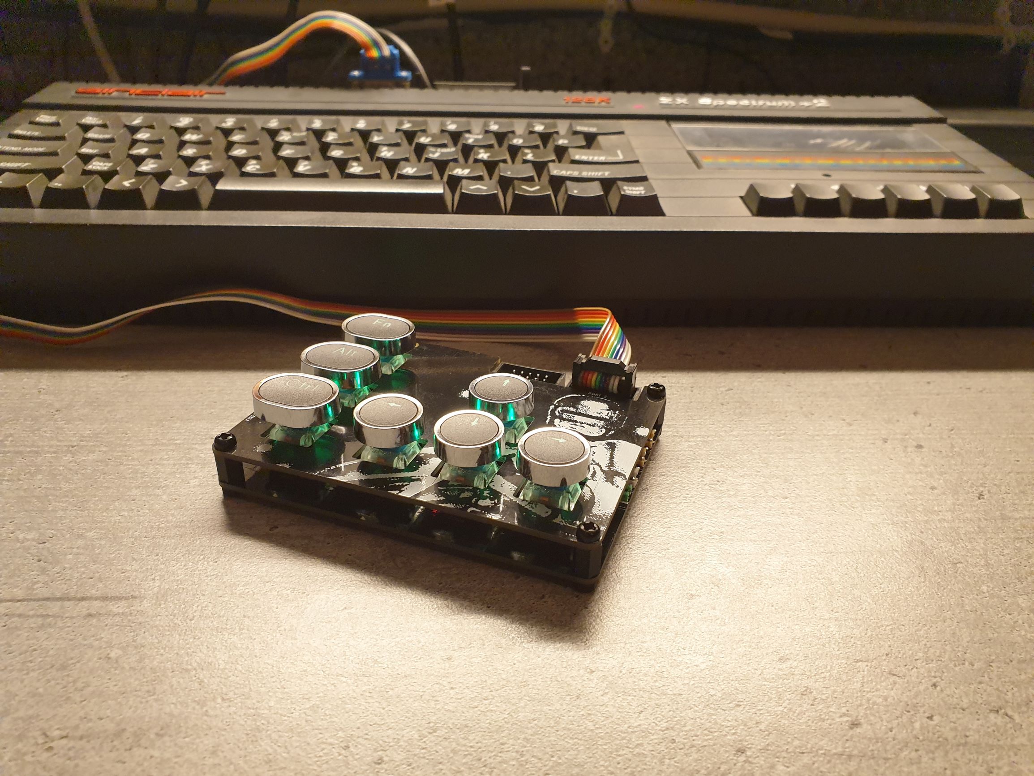
gallery/kempston_system.jpg
