tebl/C64-JoyKEY/gallery/msx_system.jpg

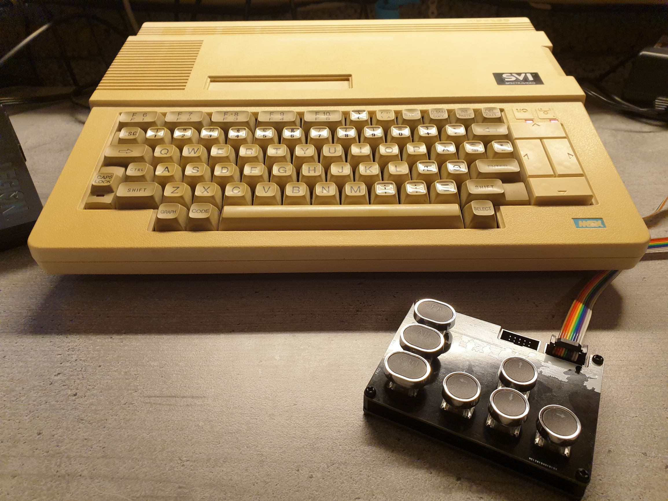
gallery/msx_system.jpg
