tebl/C64-JoyKEY/gallery/NEC PC Engine.png

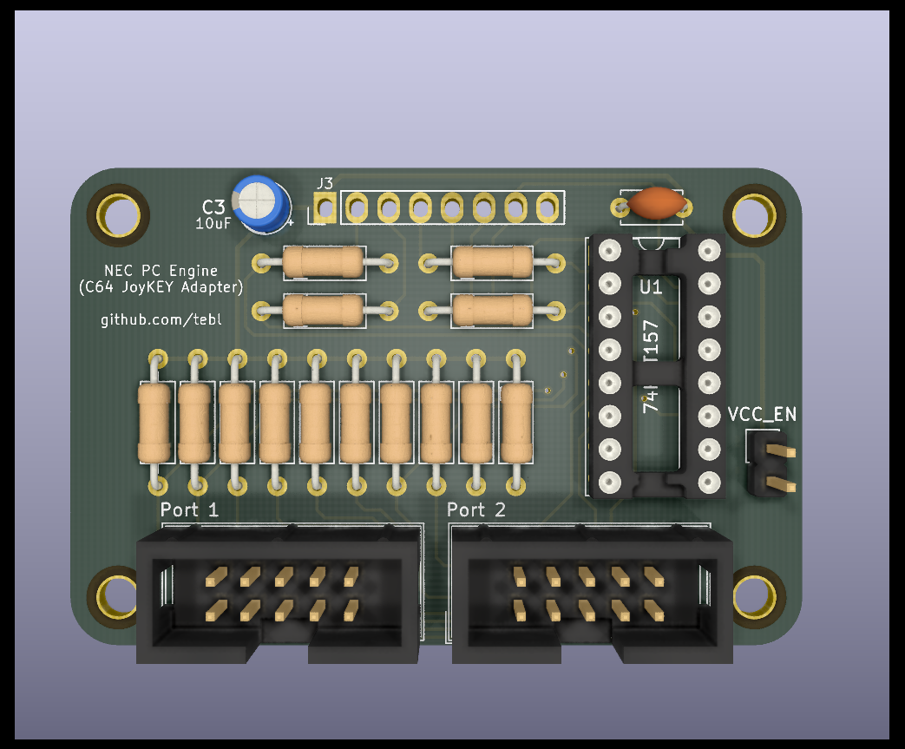
gallery/NEC PC Engine.png
