tebl/C64-JoyKEY/gallery/NES.png

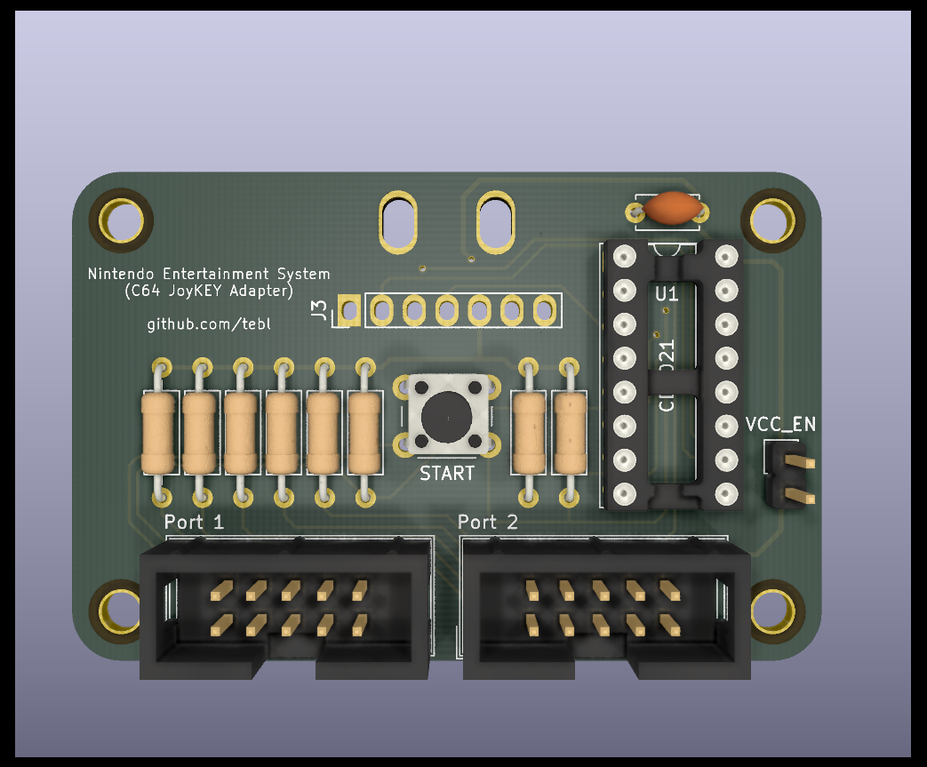
gallery/NES.png
