tebl/C64-JoyKEY/gallery/smd_adapter.jpg

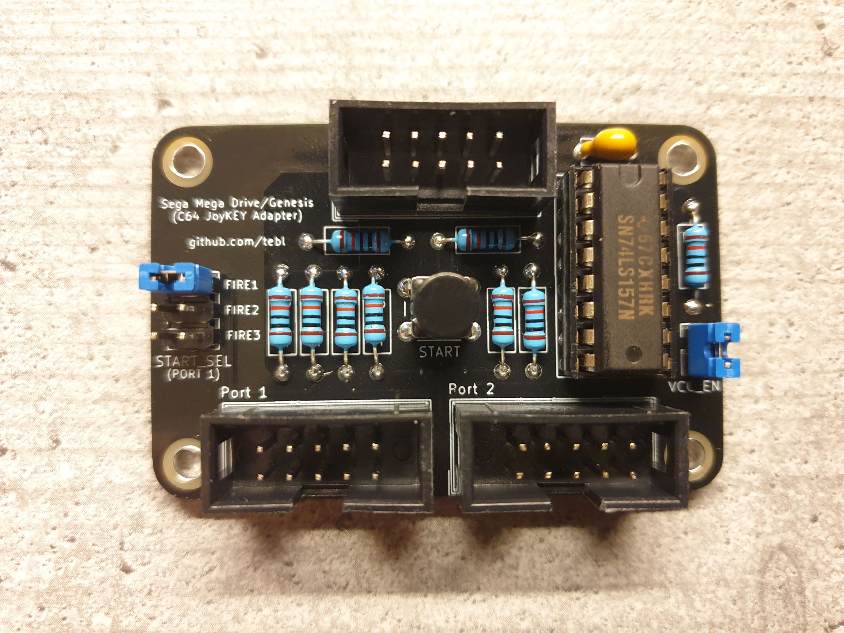
gallery/smd_adapter.jpg
