tebl/C64-JoyKEY/gallery/build/adapter9_2040/021.jpg

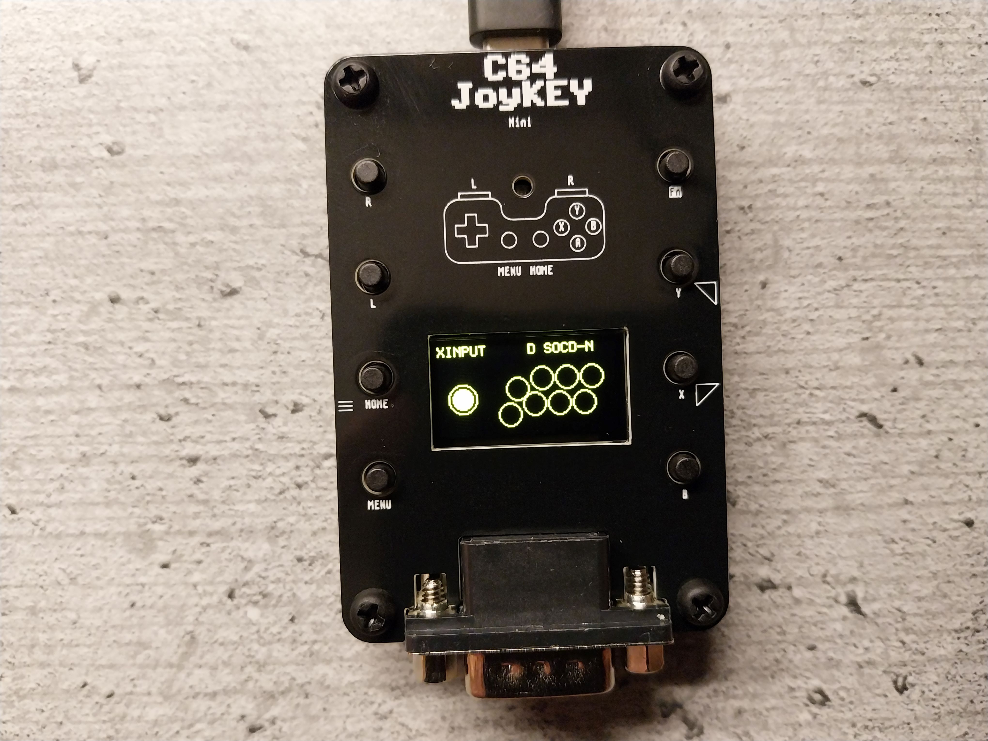
gallery/build/adapter9_2040/021.jpg
