tebl/C64-JoyKEY/gallery/build/adapter9_2040/030.jpg

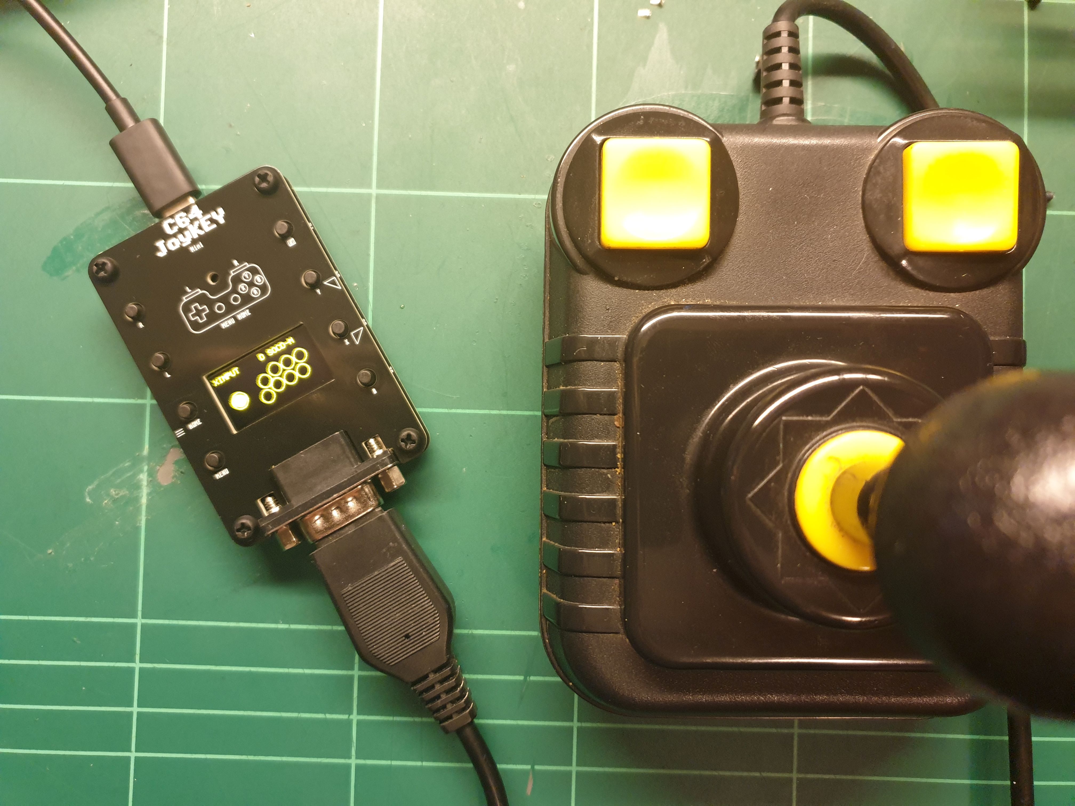
gallery/build/adapter9_2040/030.jpg
