tebl/C64-JoyKEY/gallery/build/arcade_2040/001.jpg

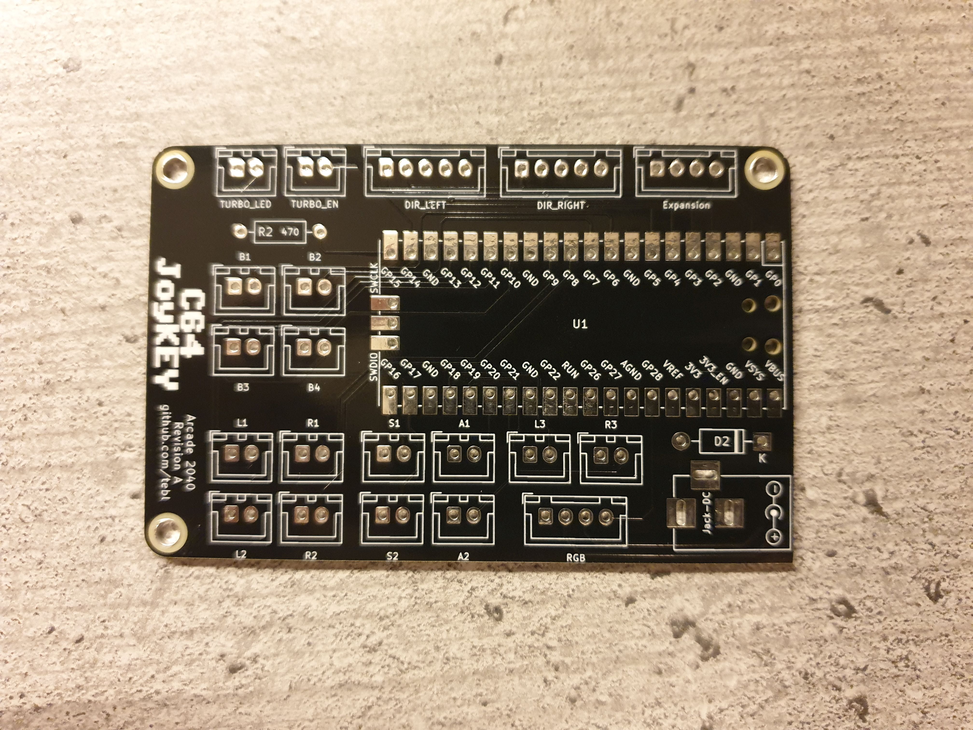
gallery/build/arcade_2040/001.jpg
