tebl/C64-JoyKEY/gallery/build/arcade_2040/002.jpg

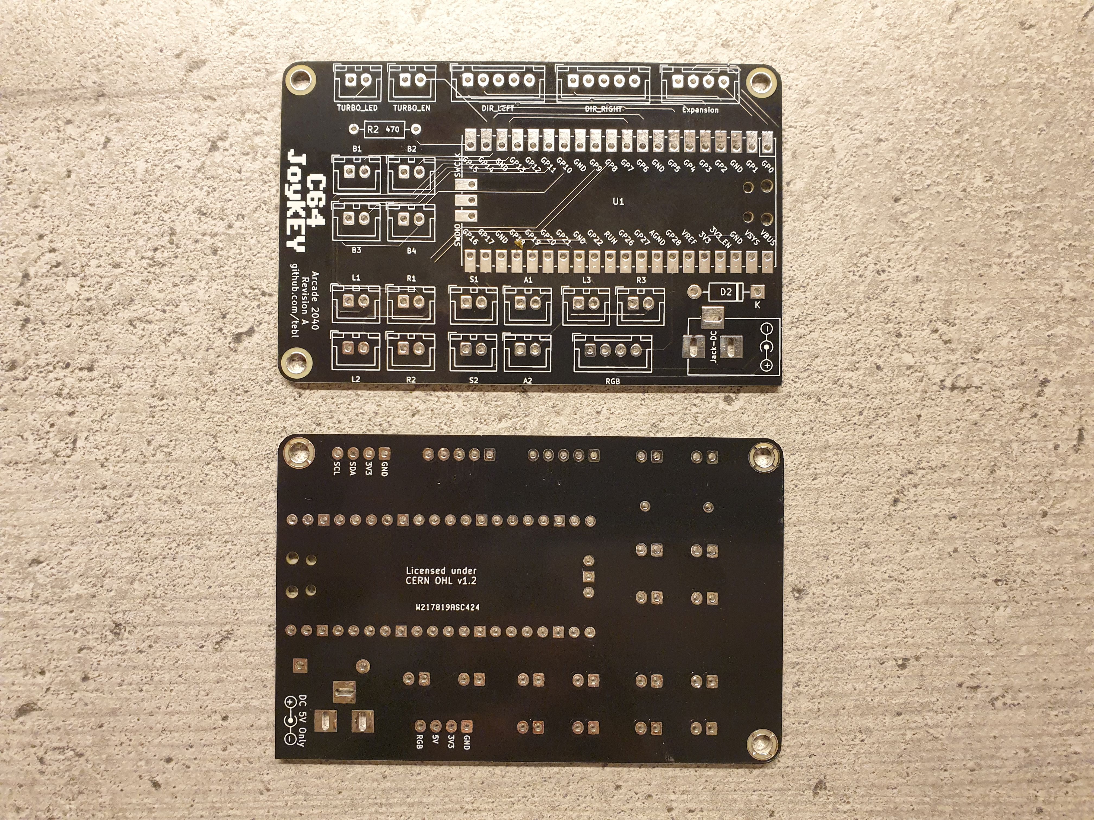
gallery/build/arcade_2040/002.jpg
