tebl/C64-JoyKEY/gallery/build/arcade_2040/015.jpg

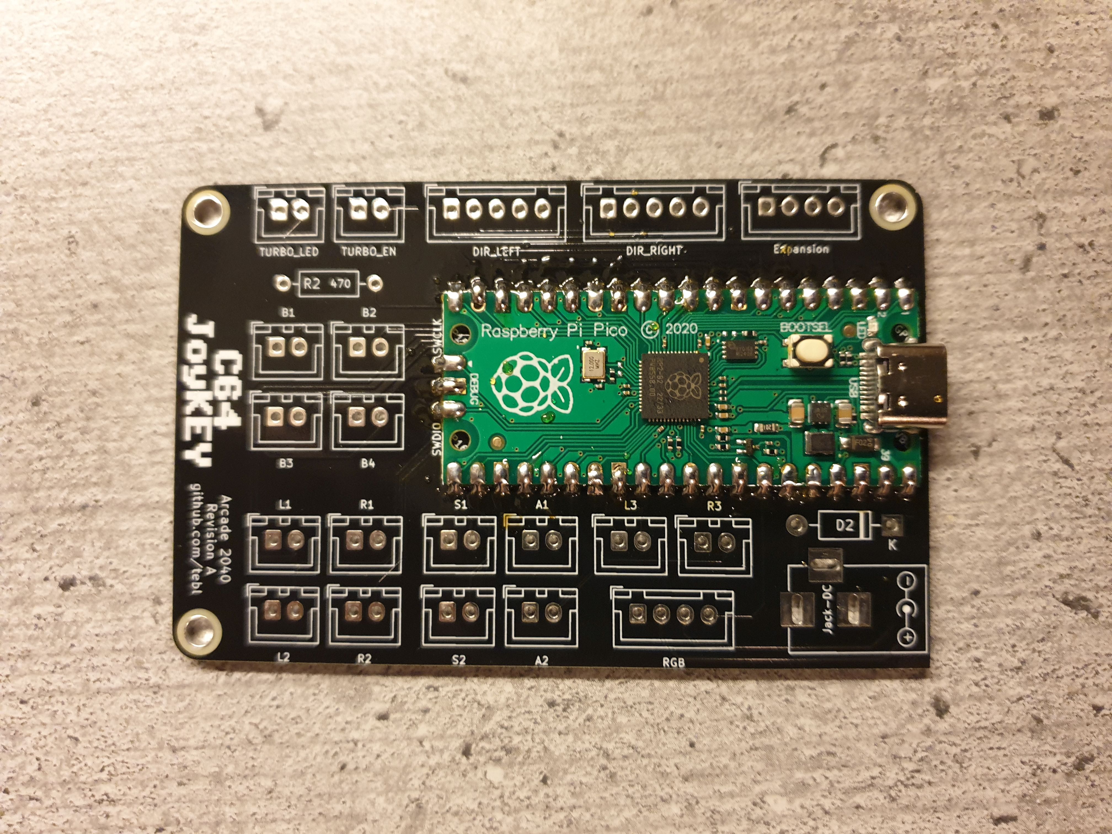
gallery/build/arcade_2040/015.jpg
