tebl/C64-JoyKEY/gallery/build/arcade_2040/020.jpg

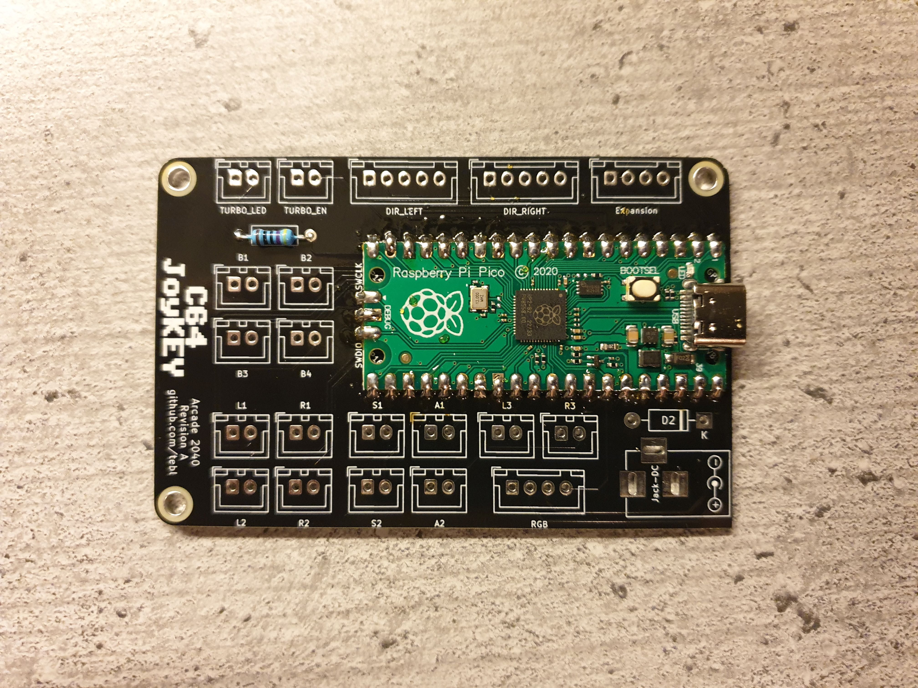
gallery/build/arcade_2040/020.jpg
