tebl/C64-JoyKEY/gallery/build/arcade_2040/025.jpg

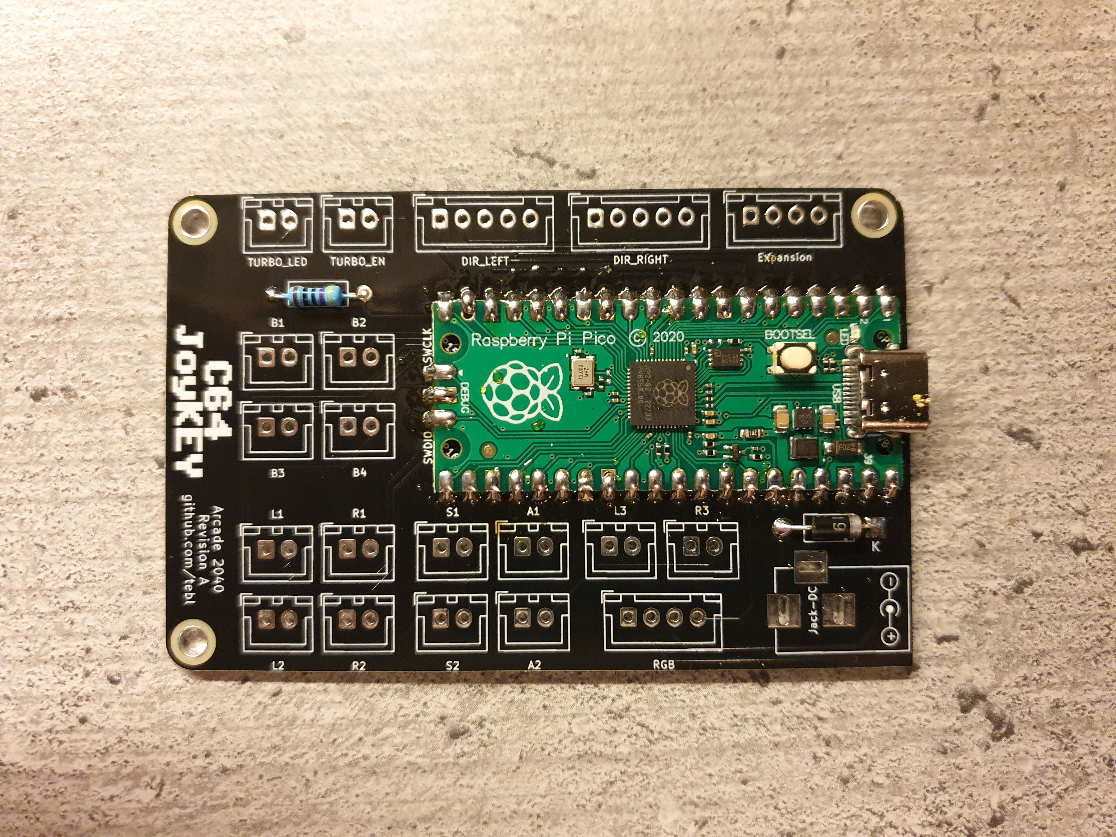
gallery/build/arcade_2040/025.jpg
