tebl/C64-JoyKEY/gallery/build/arcade_2040/030.jpg

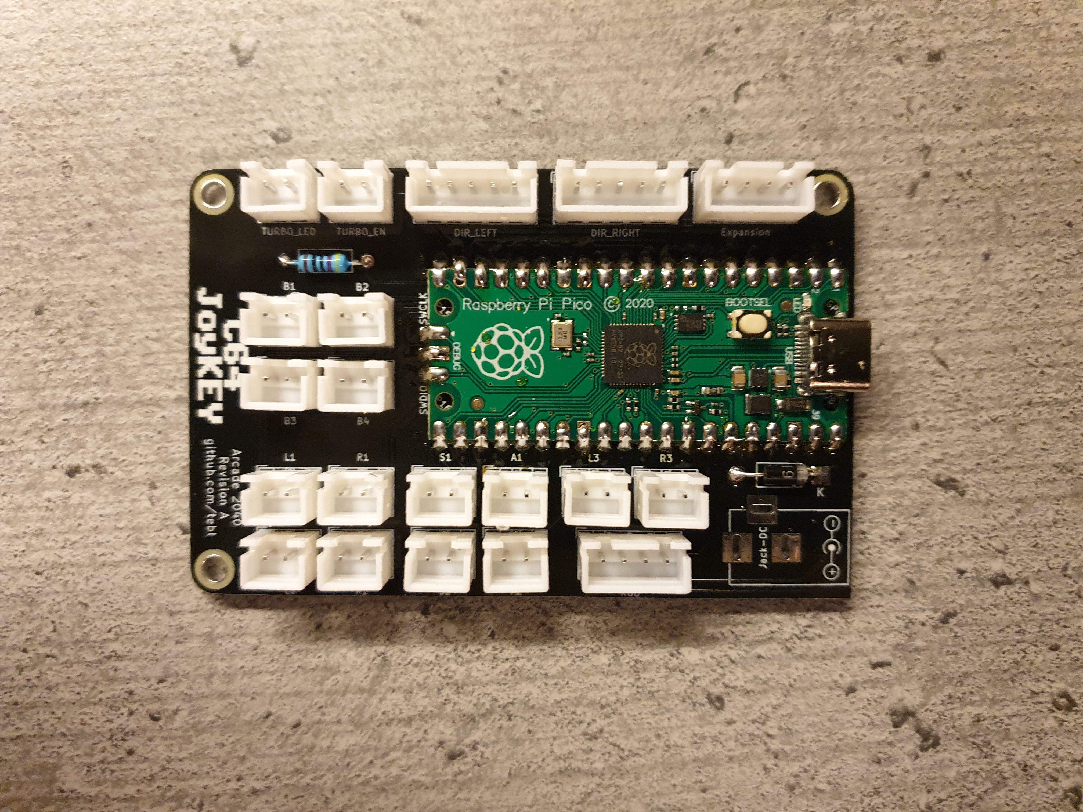
gallery/build/arcade_2040/030.jpg
