tebl/C64-JoyKEY/gallery/build/arcade_2040/035.jpg

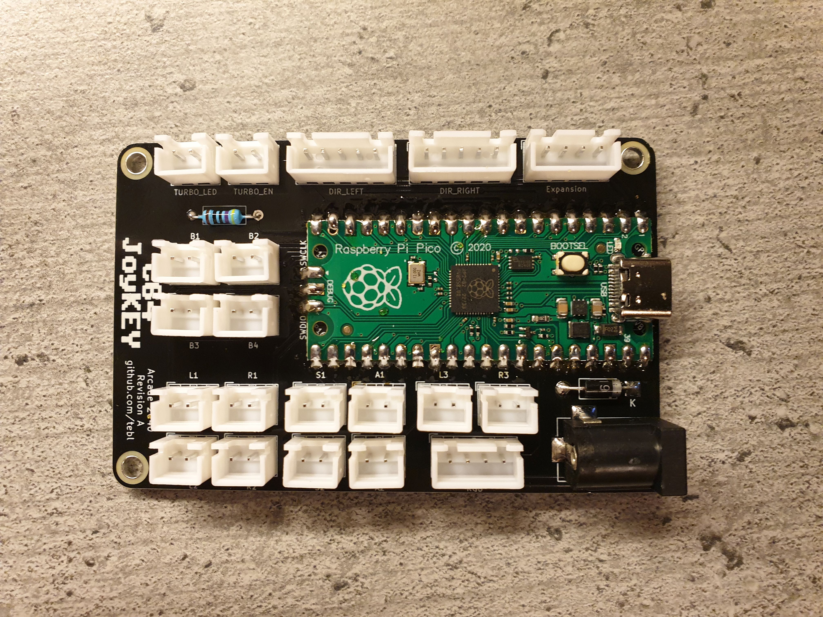
gallery/build/arcade_2040/035.jpg
