tebl/C64-JoyKEY/gallery/build/arcade_2040/050.jpg

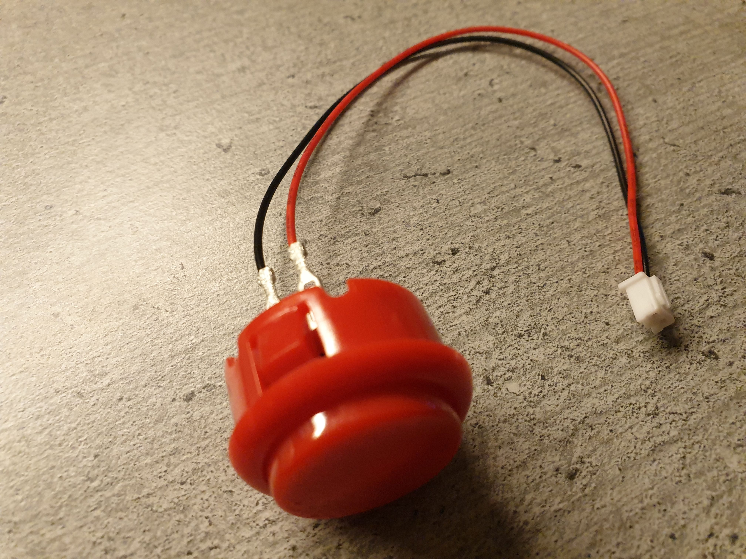
gallery/build/arcade_2040/050.jpg
