tebl/C64-JoyKEY/gallery/build/arcade_2040/055.jpg

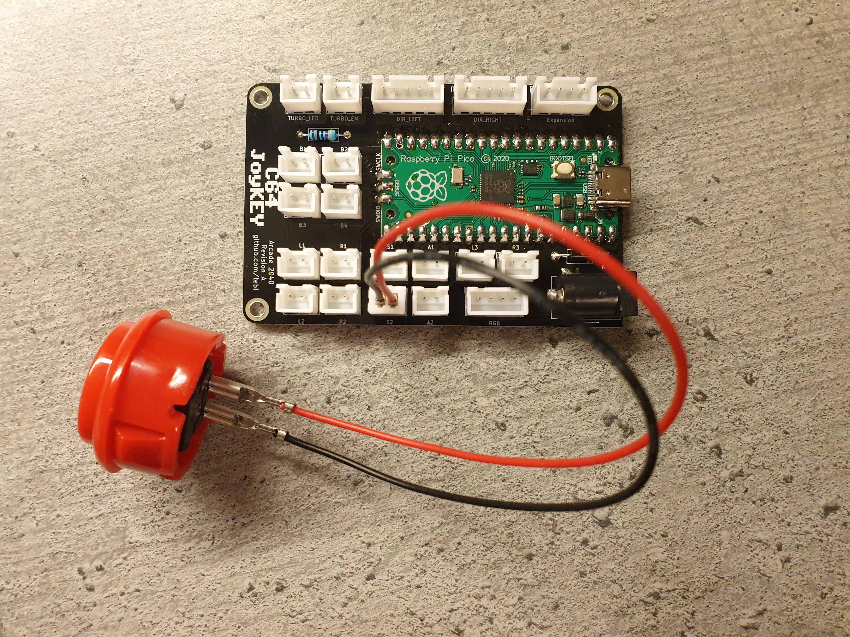
gallery/build/arcade_2040/055.jpg
