tebl/C64-JoyKEY/gallery/build/c64_joykey_2040/015.jpg

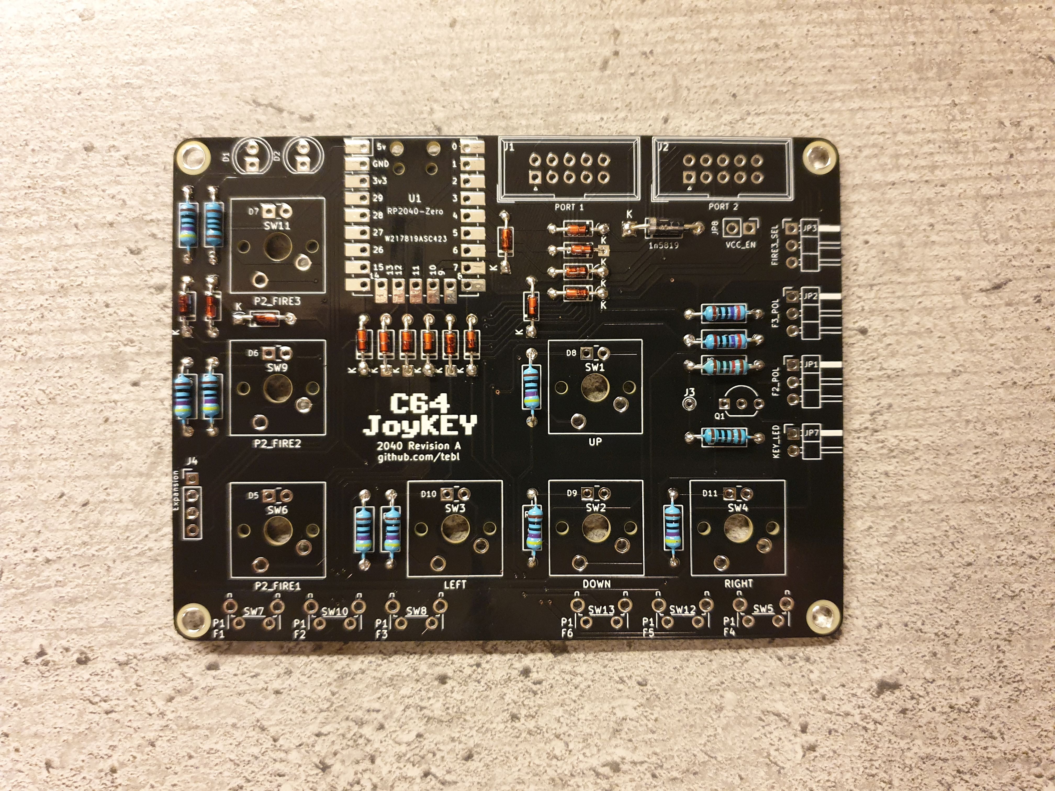
gallery/build/c64_joykey_2040/015.jpg
