tebl/C64-JoyKEY/gallery/build/c64_joykey_2040/035.jpg

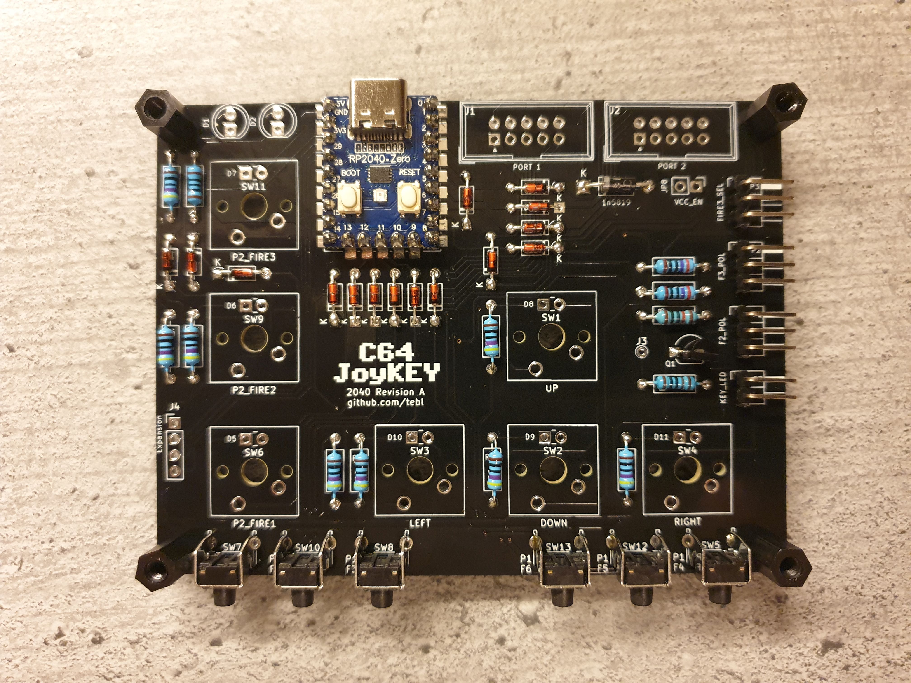
gallery/build/c64_joykey_2040/035.jpg
