tebl/C64-JoyKEY/gallery/build/c64_joykey_2040/045.jpg

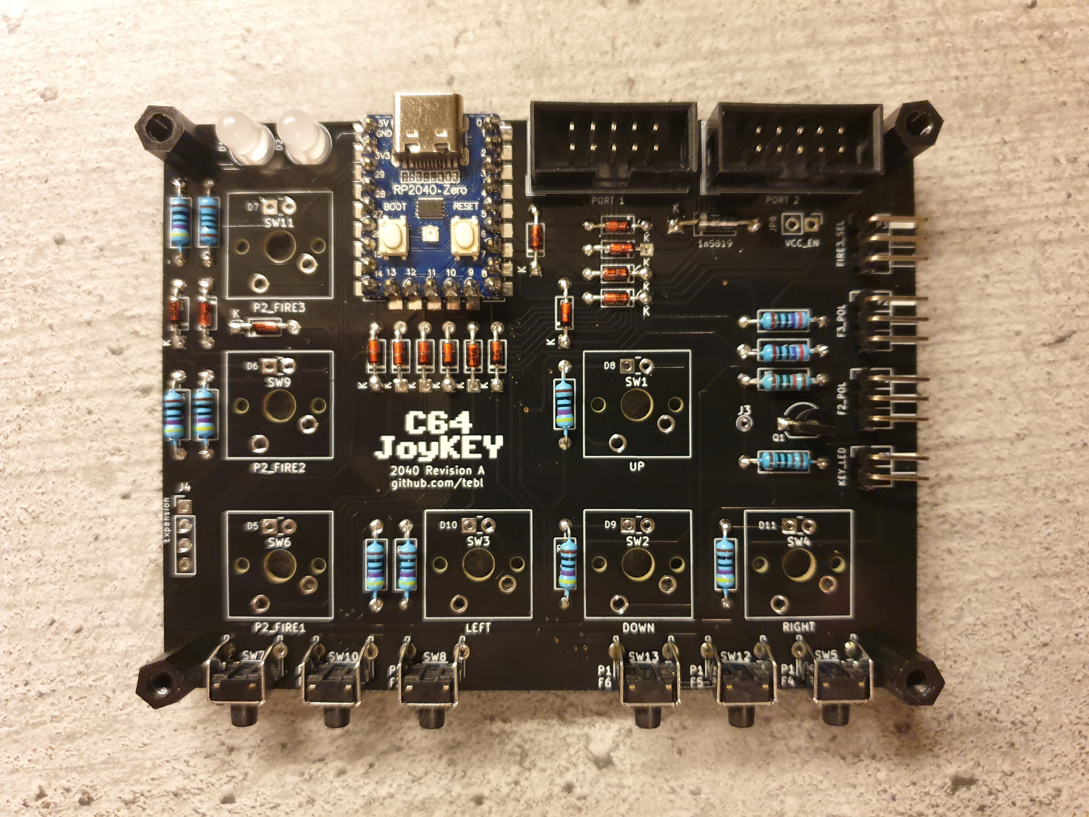
gallery/build/c64_joykey_2040/045.jpg
