tebl/C64-JoyKEY/gallery/build_022.jpg

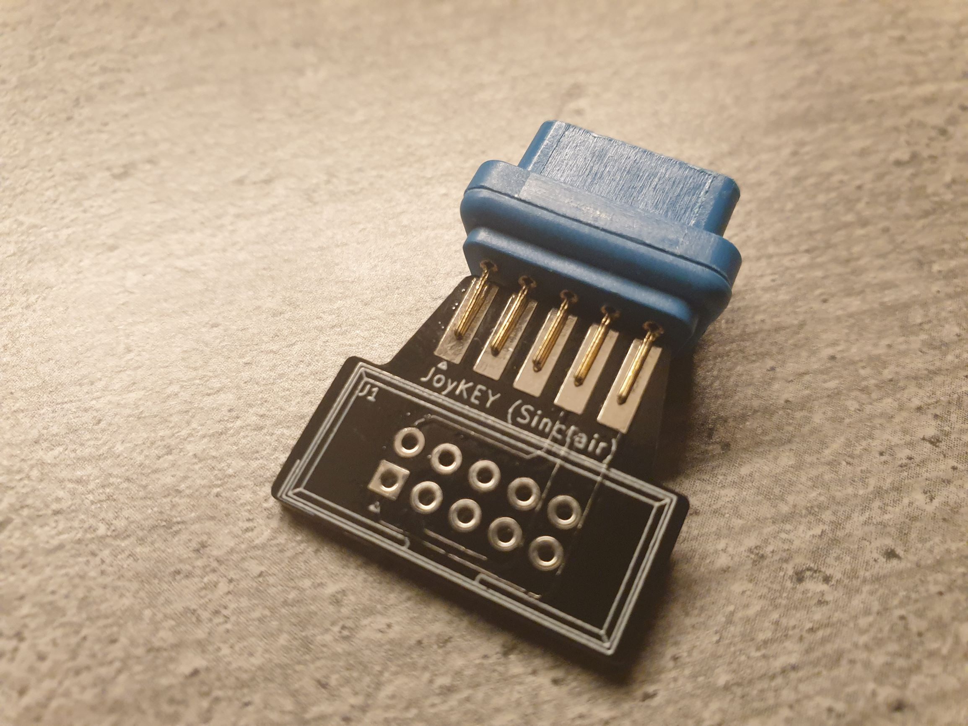
gallery/build_022.jpg
