tebl/C64-JoyKEY/gallery/build_023.jpg

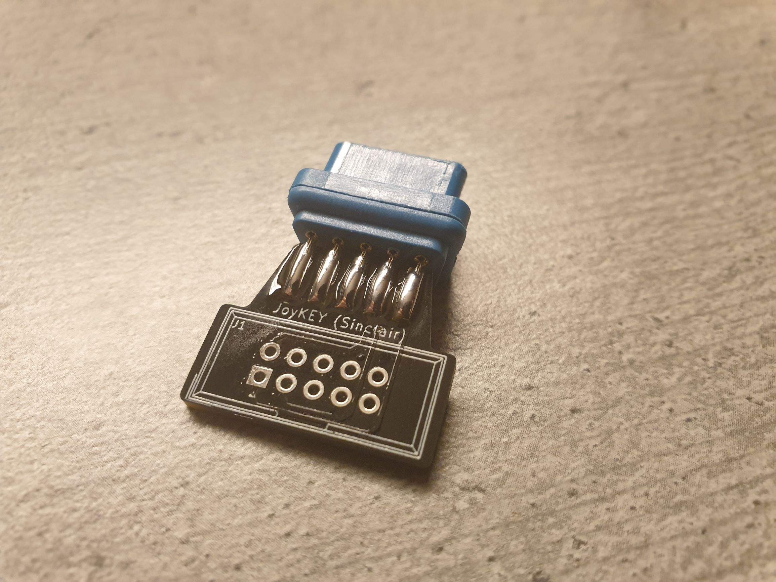
gallery/build_023.jpg
