tebl/C64-JoyKEY/gallery/build_arcade_007.jpg

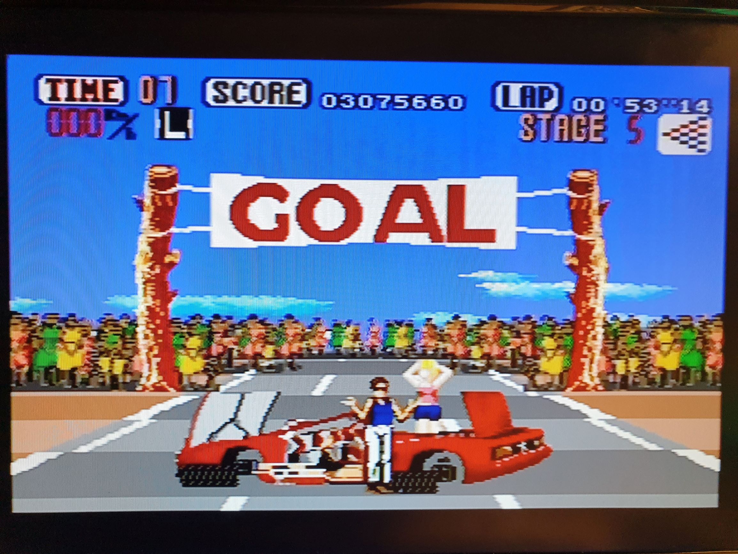
gallery/build_arcade_007.jpg
