tebl/C64-JoyKEY/documentation/schematic/adapters/Sega Mega Drive.pdf

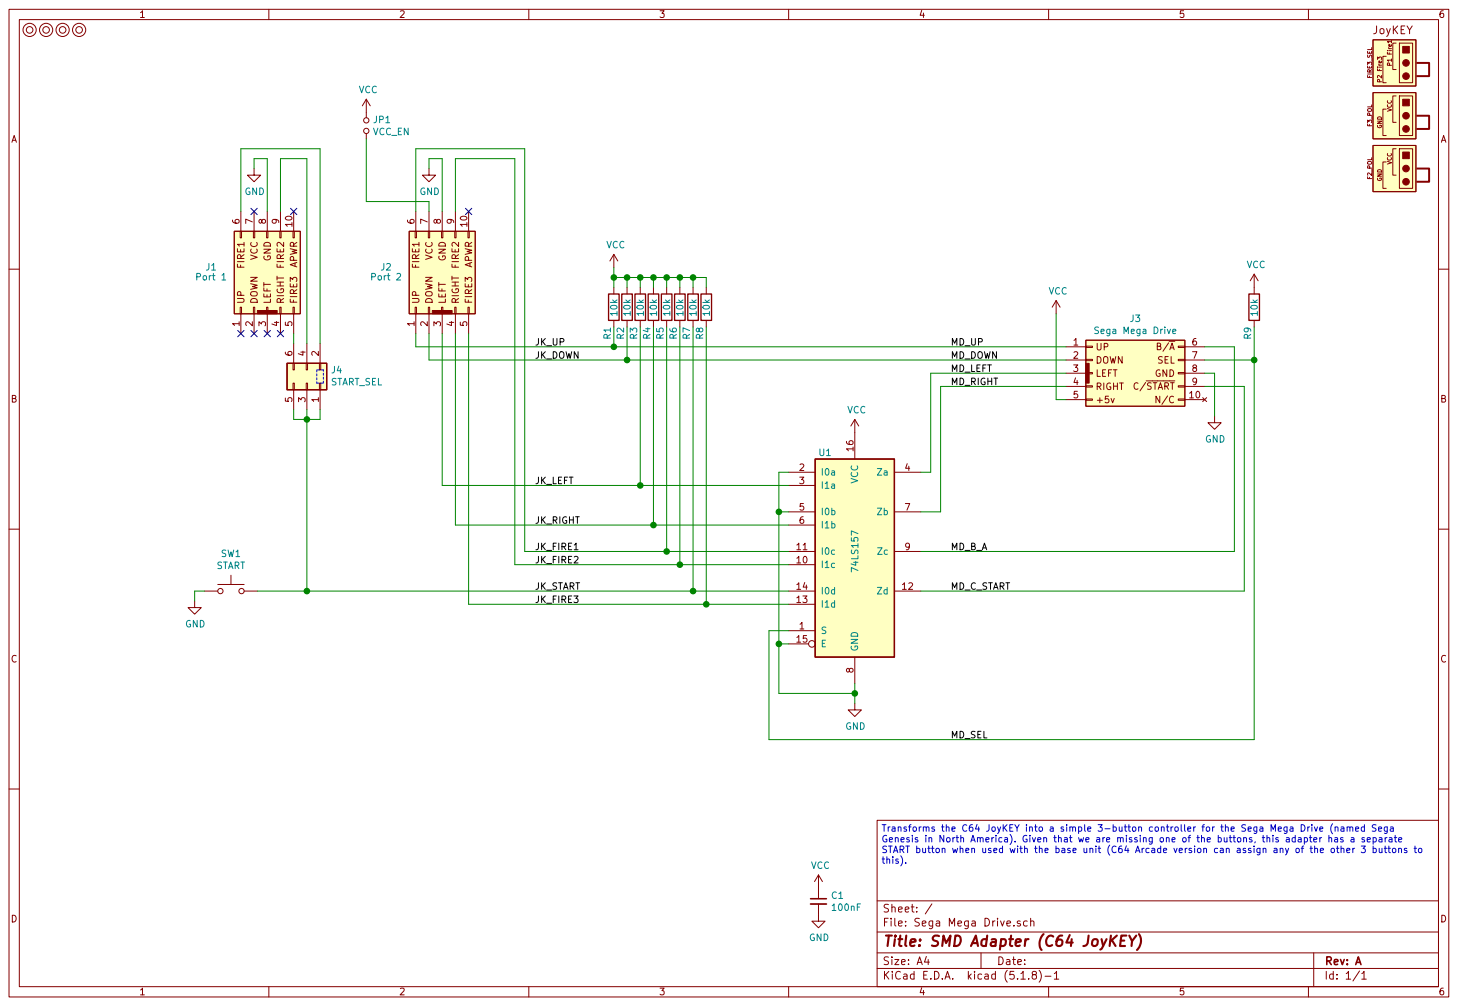
[picture p196: page 1]

JK_DOWN | | 2 | 7

File: Sega Mega Drive.sch Sheet: / GND

Transforms the C64 JoyKEY into a simple 3-button controller for the Sega Mega Drive (named Sega
Genesis in North America). Given that we are missing one of the buttons, this adapter has a separate
START button when used with the base unit (C64 Arcade version can assign any of the other 3 buttons to
this).

Id: 1/1 Title: SMD Adapter (C64 JoyKEY)
