tebl/C64-JoyKEY/documentation/schematic/adapters/IDC to DB9.pdf

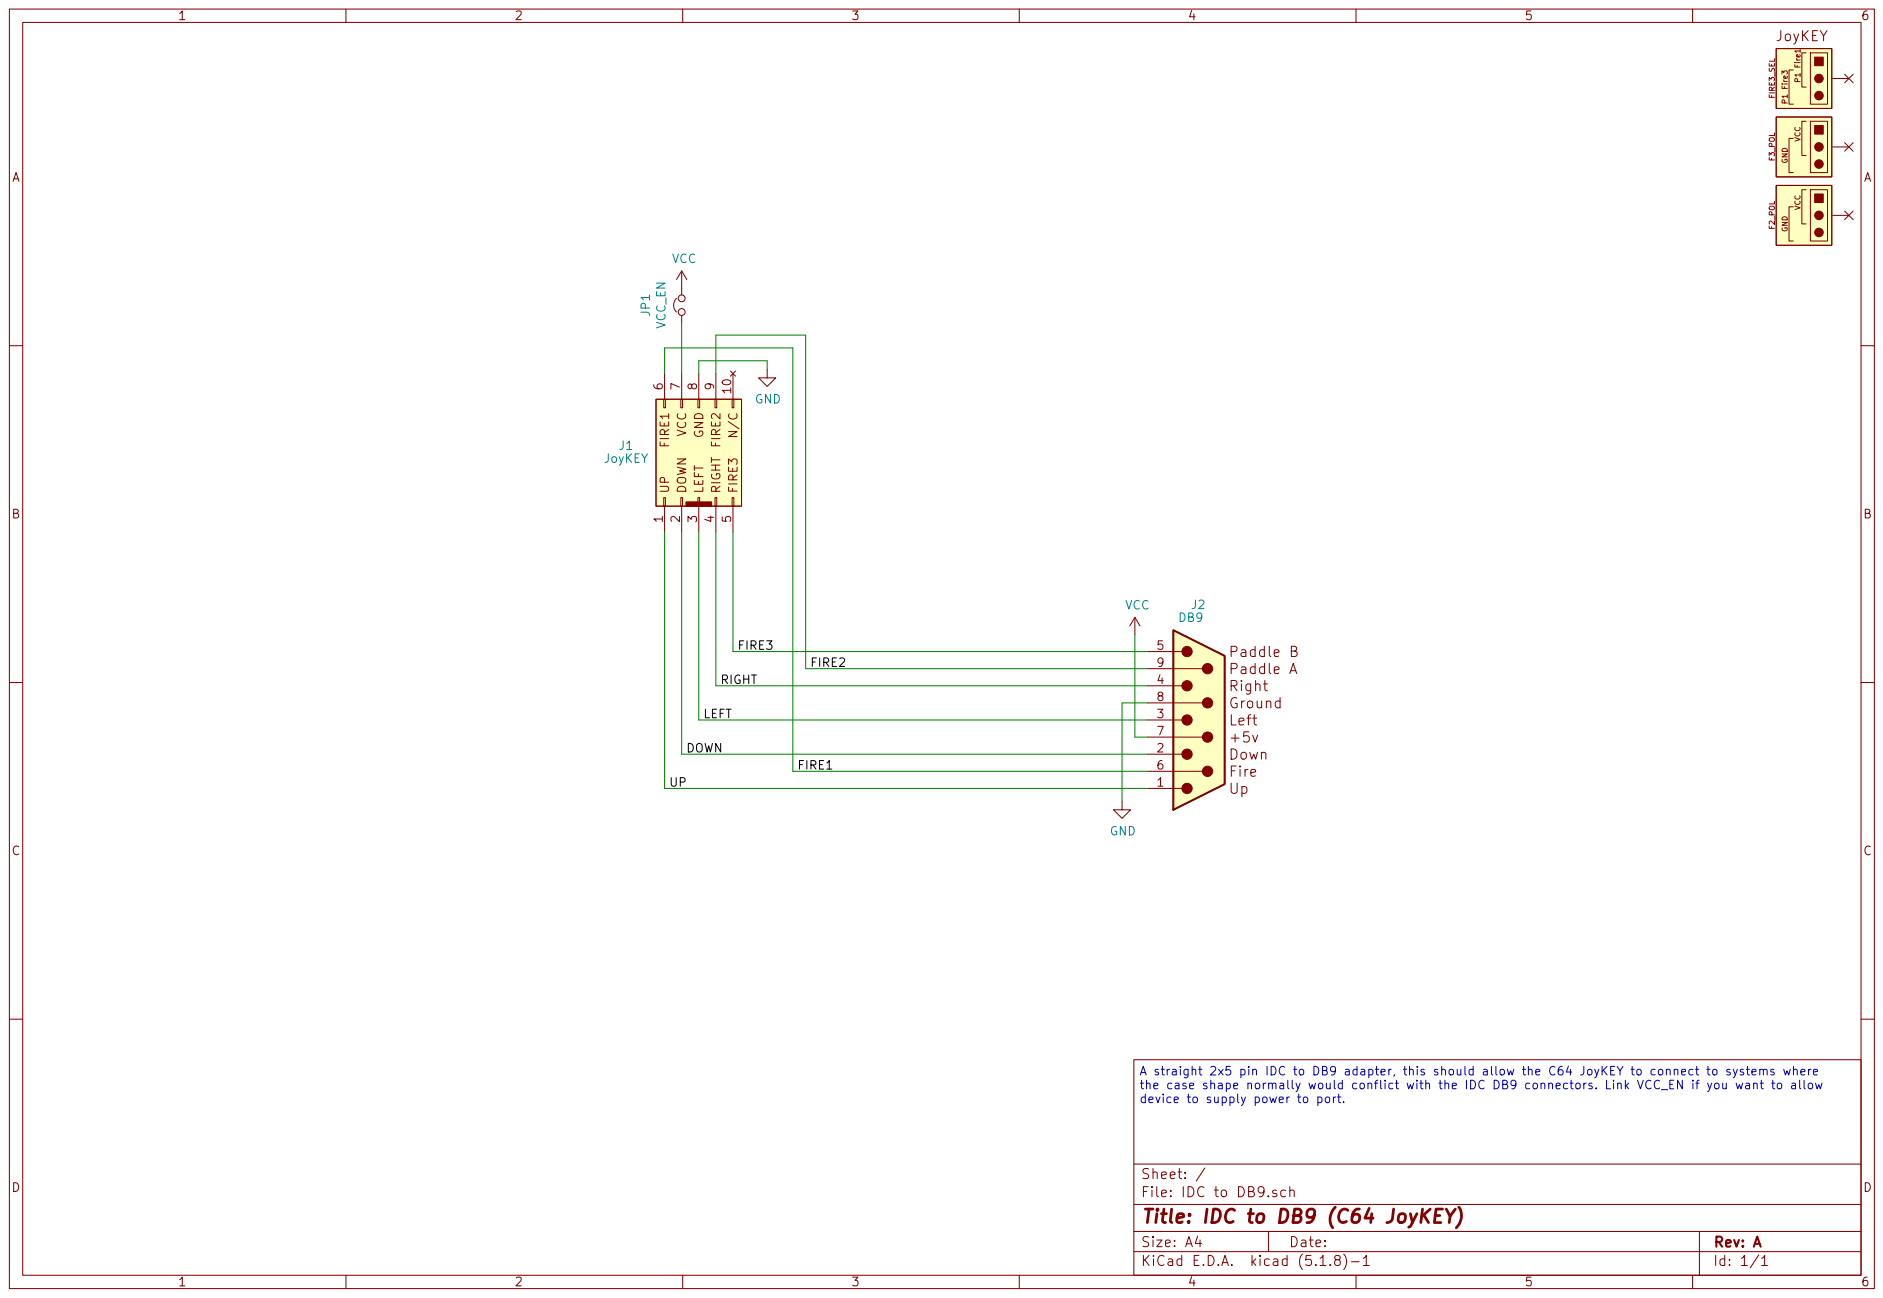
[picture p197: page 1]

the case shape normally would conflict with the IDC DB9 connectors. Link VCC_EN if you want to allow
device to supply power to port.
