tebl/C64-JoyKEY/documentation/schematic/faceplates/C64 Joykey Faceplate B1.pdf

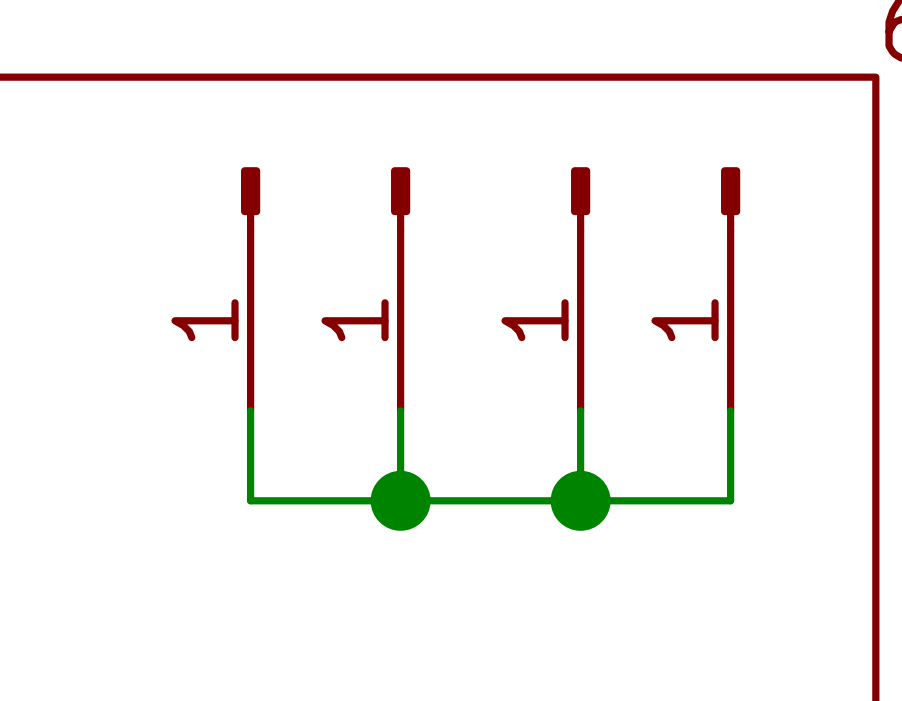
[picture p198: page 1]

It's just a faceplate, nothing to see here.

File: C64 Joykey Faceplate B1.sch Sheet: / This was designed for keycaps that don't go down past the top of the switches.

Id: 1/1 Title: C64 Joykey (Faceplate B)
