tebl/C64-JoyKEY/documentation/schematic/adapters/Sega Master System.pdf

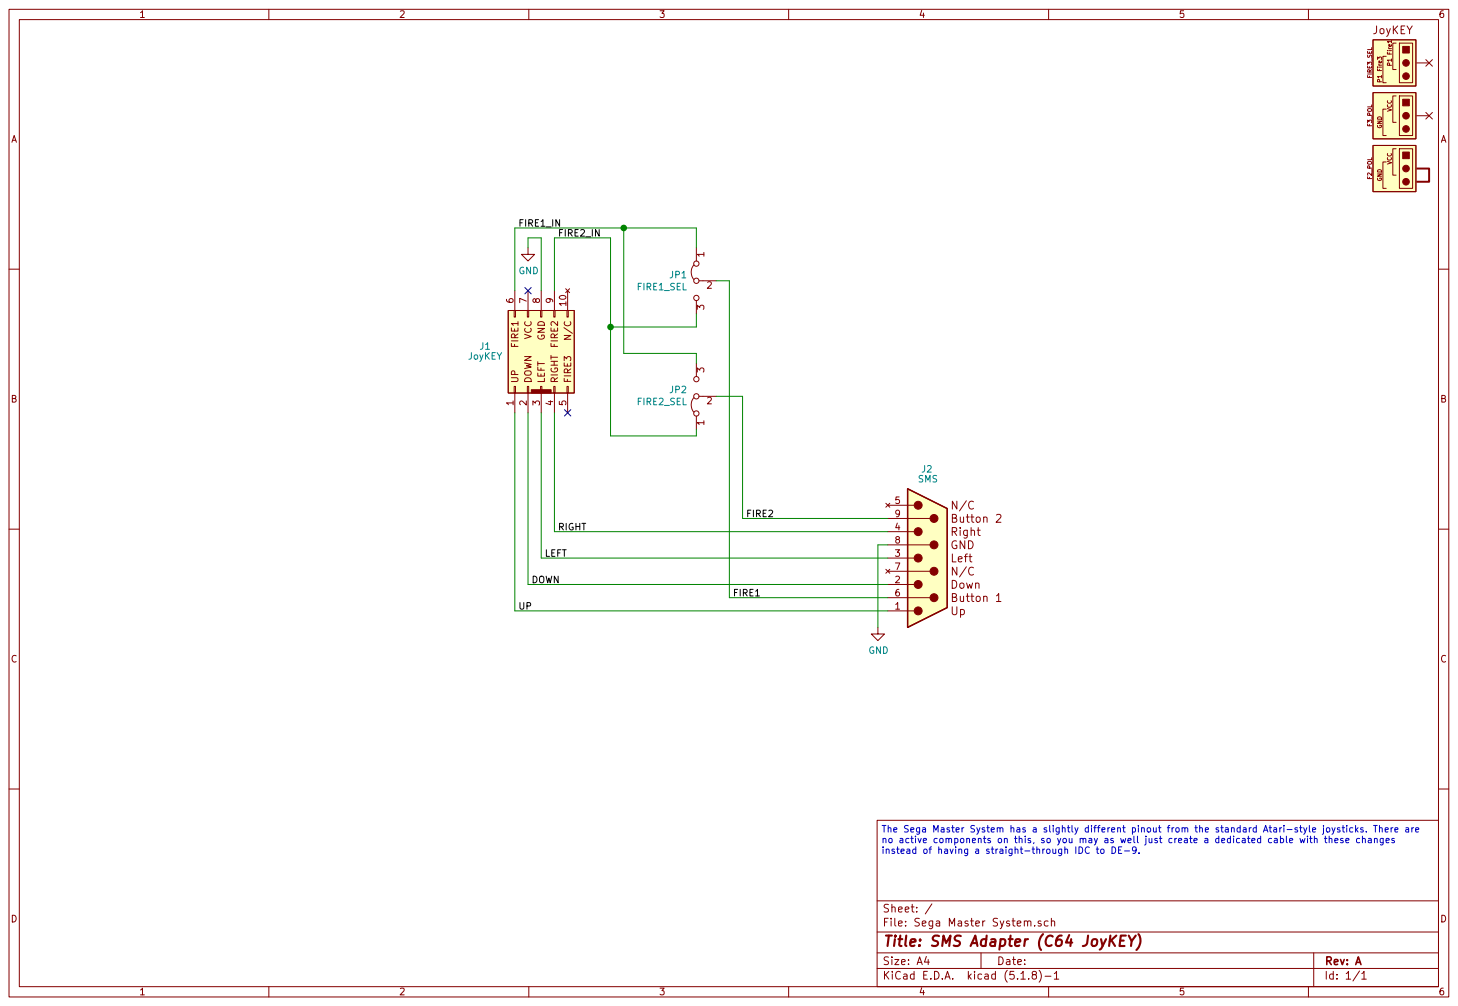
[picture p199: page 1]

The Sega Master System has a slightly different pinout from the standard Atari-style joysticks. There are
no active components on this, so you may as well just create a dedicated cable with these changes
instead of having a straight-through IDC to DE-9.

Id: 1/1 Title: SMS Adapter (C64 JoyKEY)
