tebl/C64-JoyKEY/documentation/schematic/faceplates/C64 Joykey Faceplate A1.pdf

It's just a faceplate, nothing to see here.

File: C64 Joykey Faceplate A1.sch Sheet: / This faceplate fits all MX-compatible keycaps.

Id: 1/1 Title: C64 Joykey (Faceplate A)
