tebl/C64-JoyKEY/documentation/schematic/adapters/Atari 7800.pdf

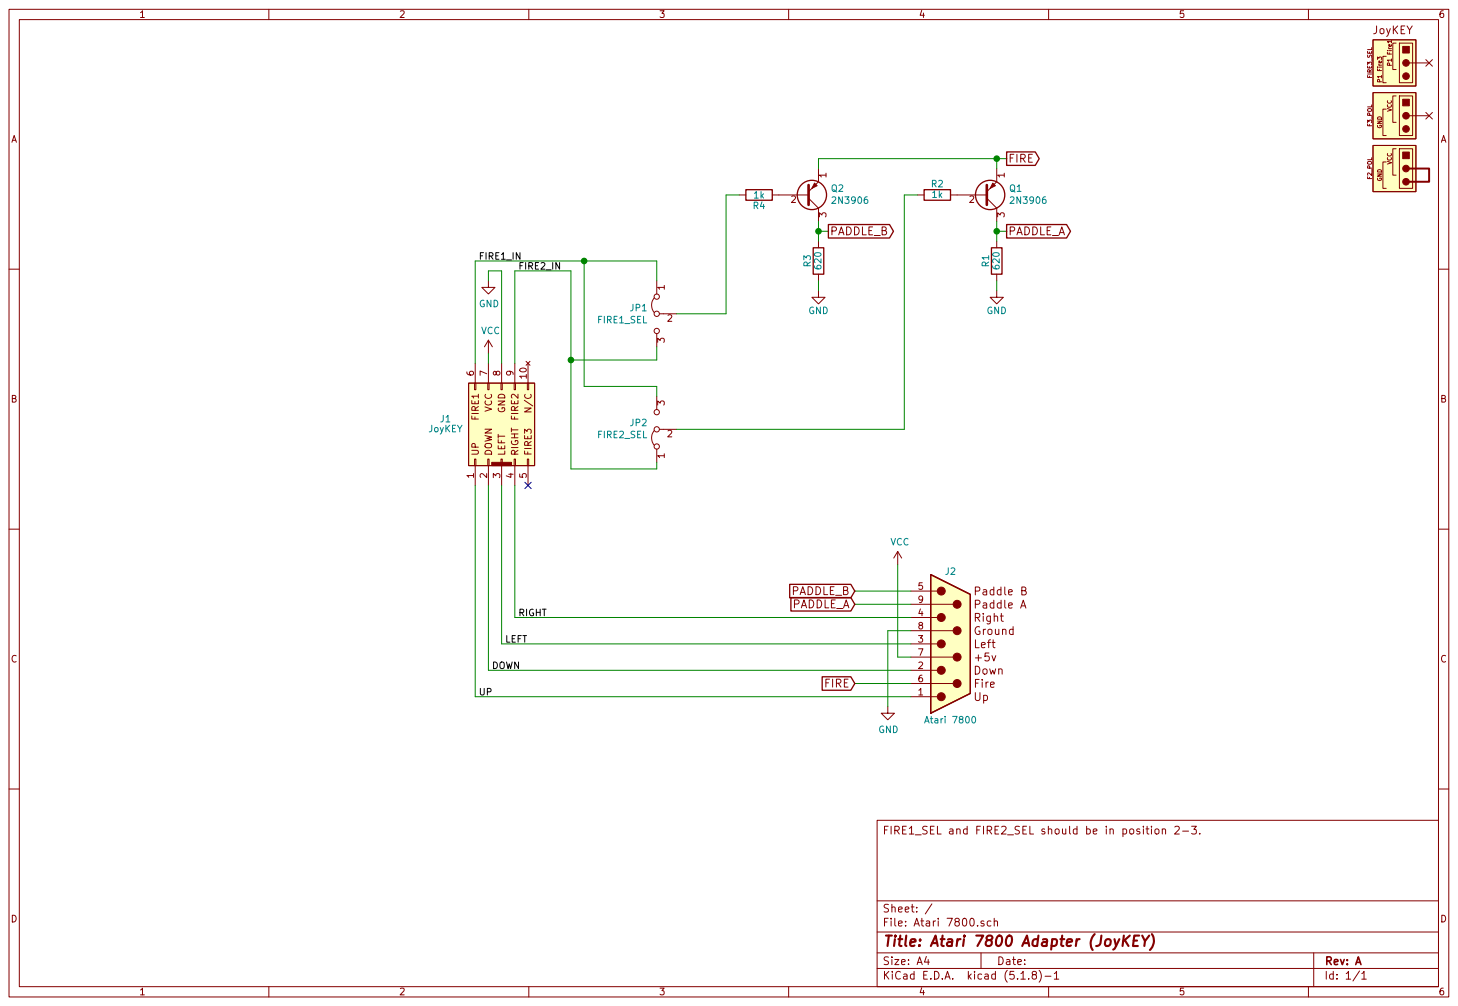
[picture p203: page 1]

Id: 1/1 Title: Atari 7800 Adapter (JoyKEY) File: Atari 7800.sch Sheet: / FIRE1_SEL and FIRE2_SEL should be in position 2-3.
