tebl/C64-JoyKEY/adapters/MSX/MSX.kicad_pcb

## KiCad design adapters/MSX/MSX.kicad_pcb (2021-03-27)

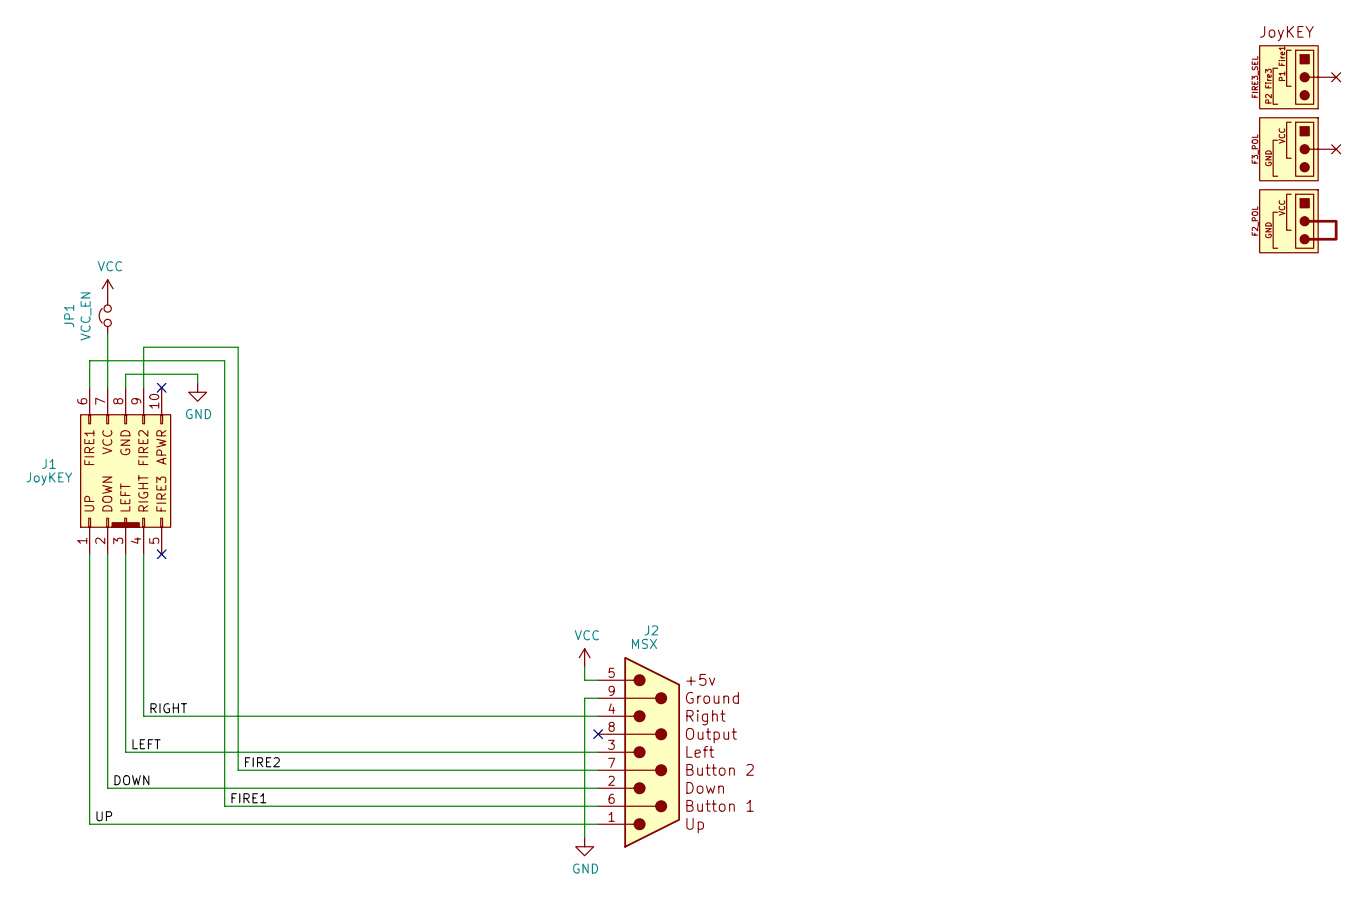
[picture p226: schematic MSX.sch, MSX (C64 JoyKEY)]

Parts:
J1: JoyKEY; IDC_Joystick
J2: MSX; DSUB-9_Female_Edge
JP1: VCC_EN; bridge

Connections:
/DOWN: J1.2, J2.2
/FIRE1: J1.6, J2.6
/FIRE2: J1.9, J2.7 (VCC)
/LEFT: J1.3, J2.3
/RIGHT: J1.4, J2.4
/UP: J1.1, J2.1
GND: J1.8, J2.9
unnamed: J1.7, JP1.1
VCC: J2.5, JP1.2

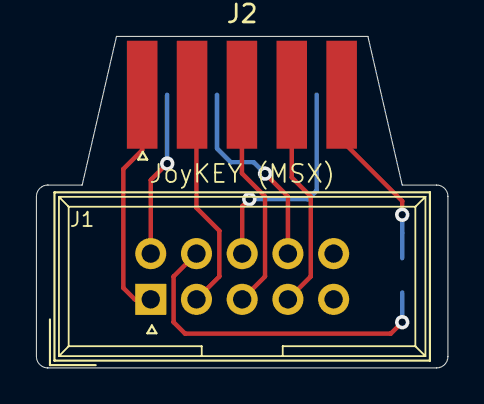
[picture p227: board MSX.kicad_pcb from above]

Board: 2 copper layers, 22.9 x 18.4 mm, 3 parts (1 on the bottom side), 9 nets.
