tebl/C64-JoyKEY/C64 SkeletonKey/C64 SkeletonKey.kicad_pcb

## KiCad design C64 SkeletonKey/C64 SkeletonKey.kicad_pcb (2021-03-21)

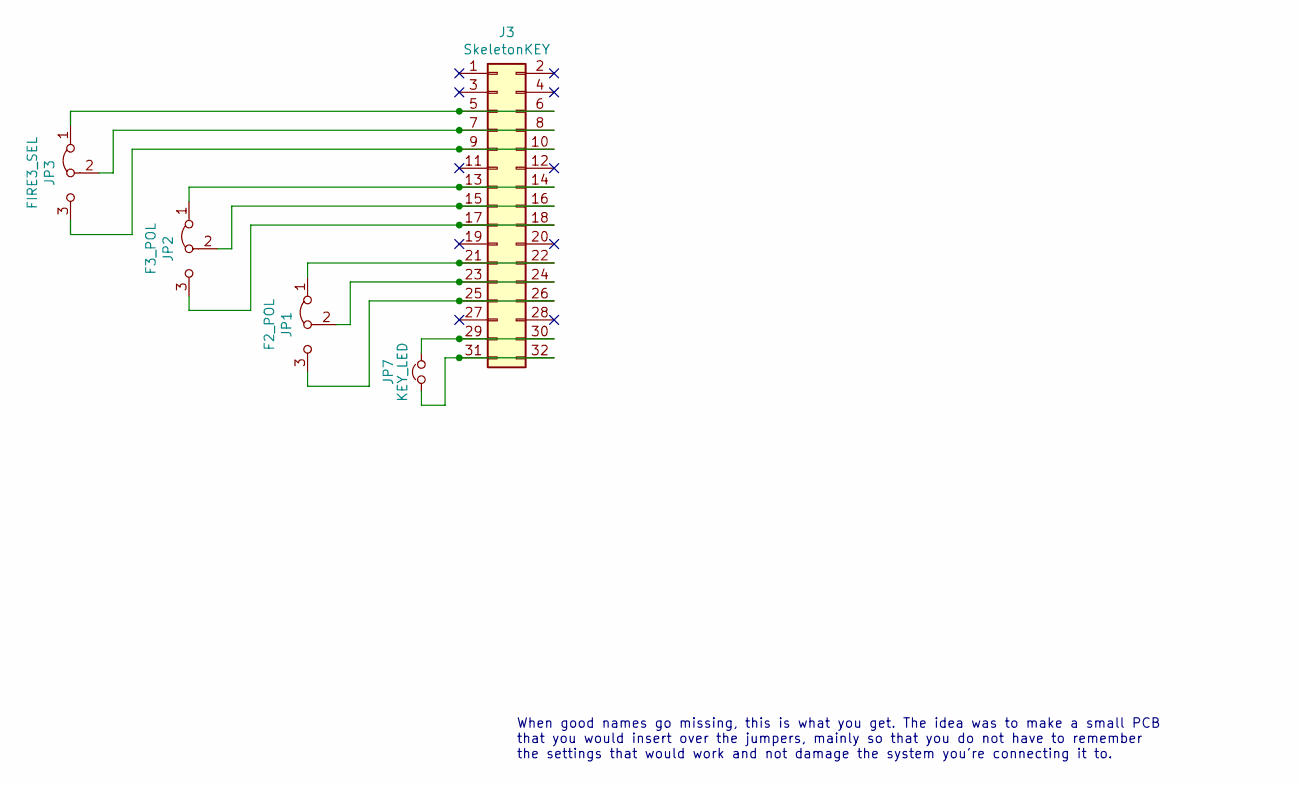
[picture p228: schematic C64 SkeletonKey.sch, C64 JoyKEY (SkeletonKEY)]

Parts:
J3: SkeletonKEY; PinHeader_2x16_P2.54mm_Vertical
JP1: F2_POL; select_r
JP2: F3_POL; select_r
JP3: FIRE3_SEL; select_r
JP7: KEY_LED; bridge_r

Connections:
unnamed: J3.5, J3.6, JP3.1 (A)
unnamed: J3.7, J3.8, JP3.2 (C)
unnamed: J3.9, J3.10, JP3.3 (B)
unnamed: J3.13, J3.14, JP2.1 (A)
unnamed: J3.15, J3.16, JP2.2 (C)
unnamed: J3.17, J3.18, JP2.3 (B)
unnamed: J3.21, J3.22, JP1.1 (A)
unnamed: J3.23, J3.24, JP1.2 (C)
unnamed: J3.25, J3.26, JP1.3 (B)
unnamed: J3.29, J3.30, JP7.1
unnamed: J3.31, J3.32, JP7.2

Notes on the sheet:
When good names go missing, this is what you get. The idea was to make a small PCB that you would insert over the jumpers, mainly so that you do not have to remember the settings that would work and not damage the system you're connecting it to.

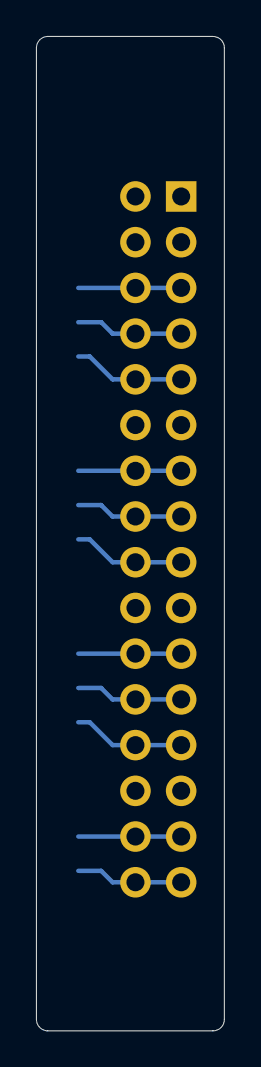
[picture p229: board C64 SkeletonKey.kicad_pcb from above]

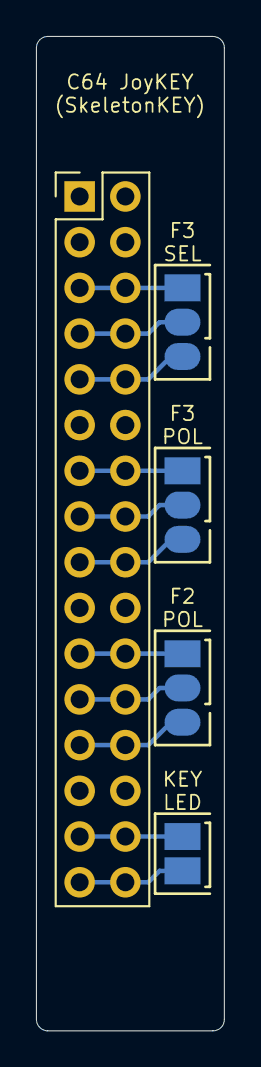
[picture p230: board C64 SkeletonKey.kicad_pcb from below]

Board: 2 copper layers, 10.4 x 55.2 mm, 5 parts (5 on the bottom side), 11 nets.
