tebl/C64-JoyKEY/adapters/Sinclair/Sinclair.kicad_pcb

## KiCad design adapters/Sinclair/Sinclair.kicad_pcb (2021-02-19)

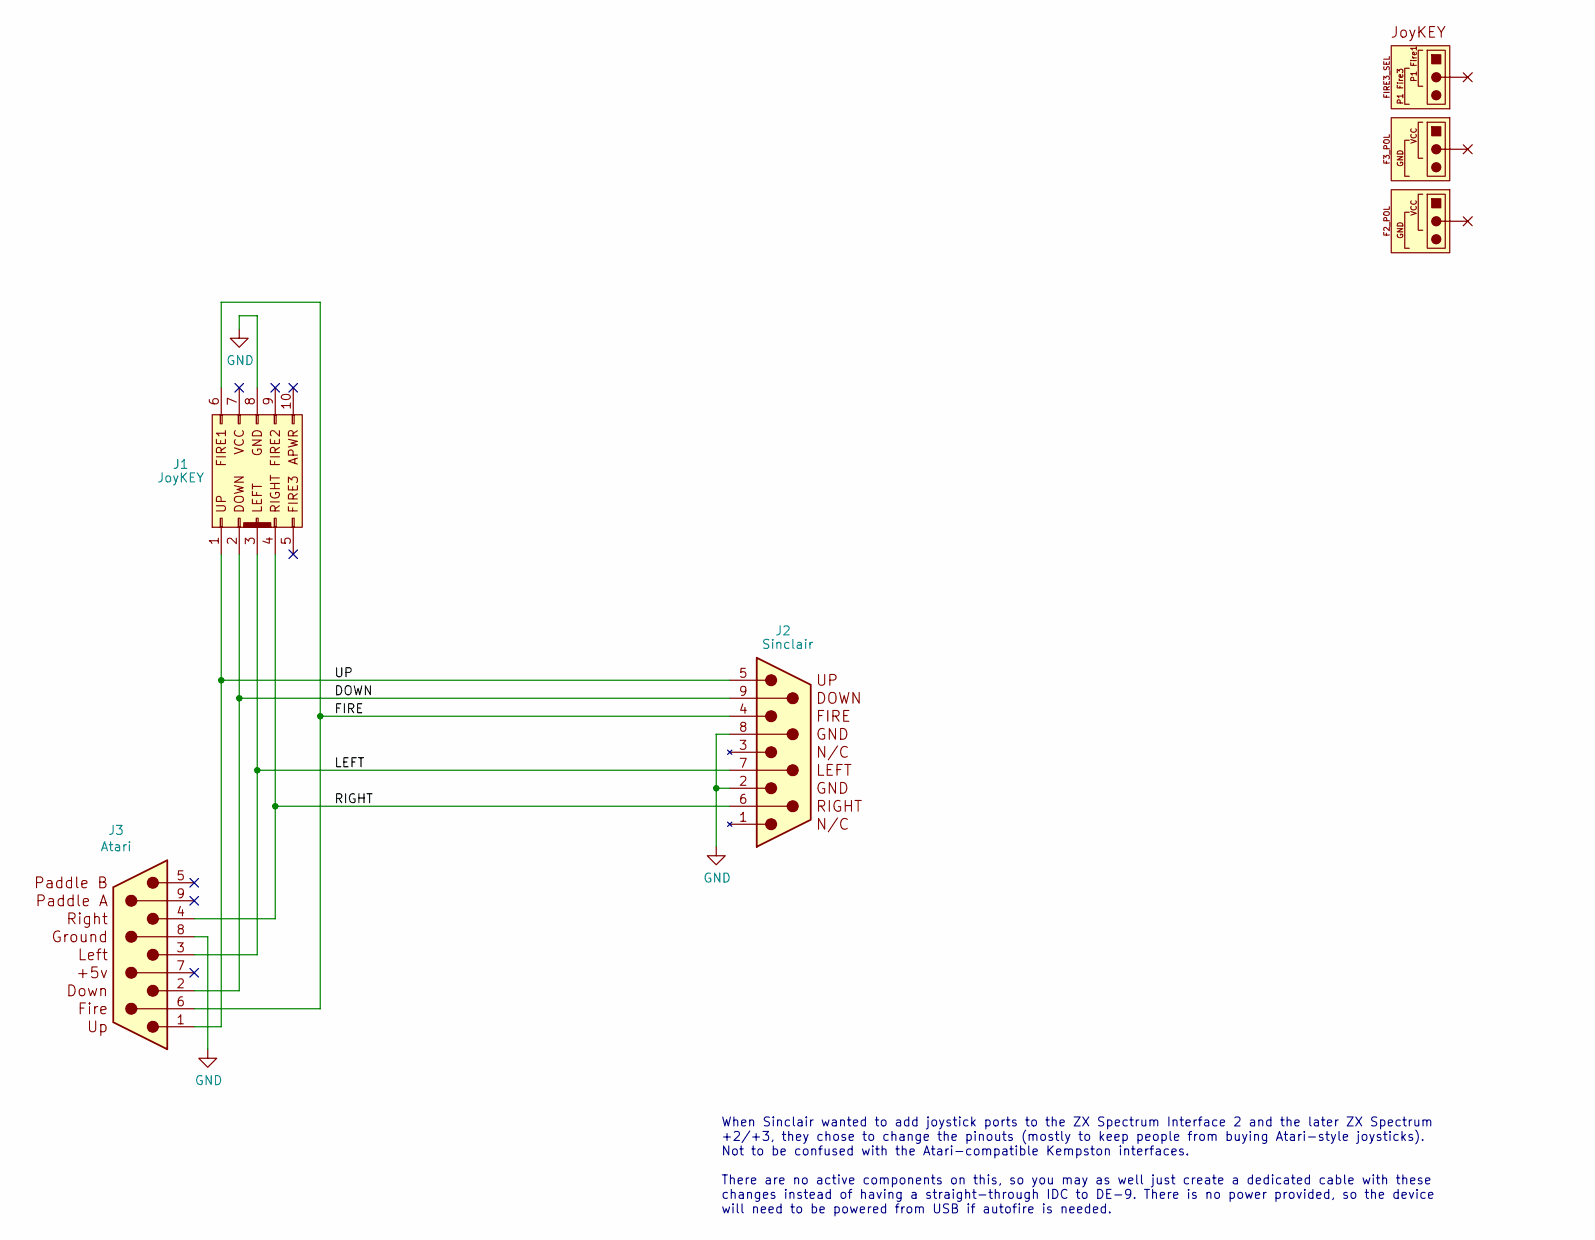
[picture p231: schematic Sinclair.sch, Sinclair Adapter (C64 JoyKEY)]

Parts:
J1: JoyKEY; IDC_Joystick
J2: Sinclair; DSUB-9_Female_Edge
J3: Atari; DSUB-9_Male_Edge

Connections:
/DOWN: J1.2, J2.9, J3.2
/FIRE: J1.6, J2.4, J3.6
/LEFT: J1.3, J2.7, J3.3
/RIGHT: J1.4, J2.6, J3.4
/UP: J1.1, J2.5, J3.1
GND: J1.8, J2.2 (GND), J2.8, J3.8 (GND)

Notes on the sheet:
When Sinclair wanted to add joystick ports to the ZX Spectrum Interface 2 and the later ZX Spectrum +2/+3, they chose to change the pinouts (mostly to keep people from buying Atari-style joysticks). Not to be confused with the Atari-compatible Kempston interfaces. There are no active components on 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

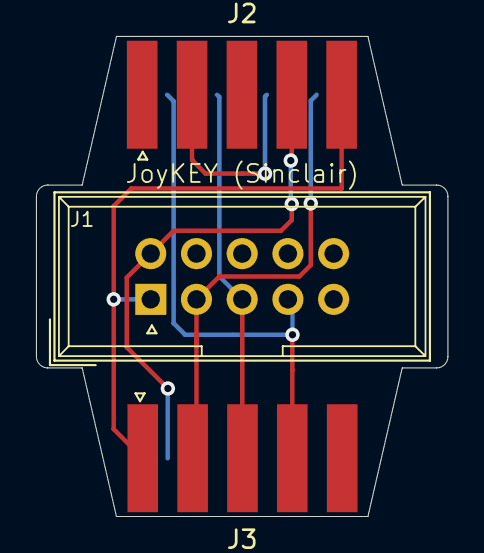
[picture p232: board Sinclair.kicad_pcb from above]

Board: 2 copper layers, 22.9 x 26.7 mm, 3 parts (0 on the bottom side), 6 nets.
