tebl/C64-JoyKEY/gallery/build/c64_joykey_2040/058.jpg

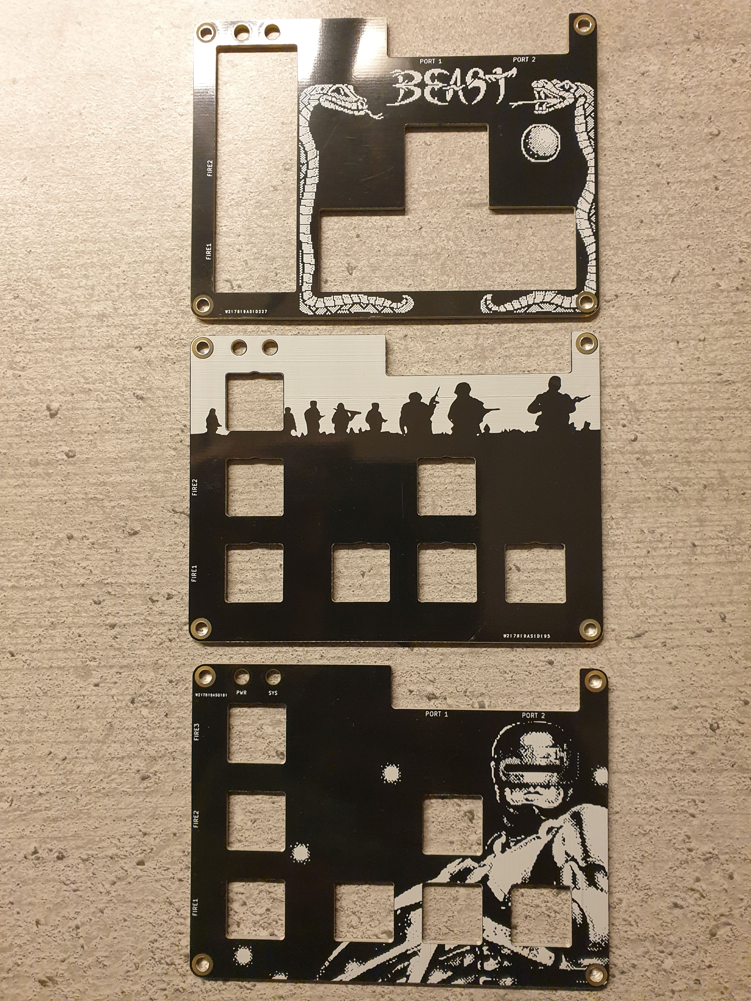
gallery/build/c64_joykey_2040/058.jpg
